SukkoPera/LittleSixteen/doc/6529_replacement_for_C16.gif

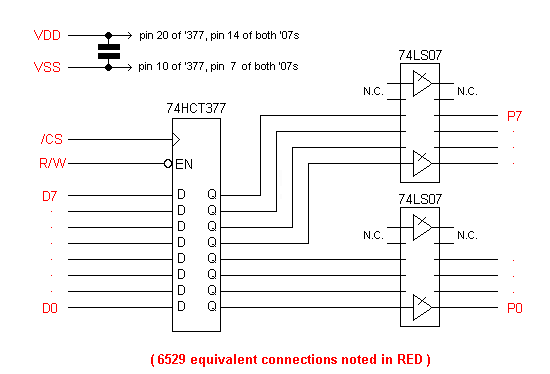
doc/6529_replacement_for_C16.gif
