SukkoPera/LittleSixteen/doc/c16-251788-1of3-left.gif

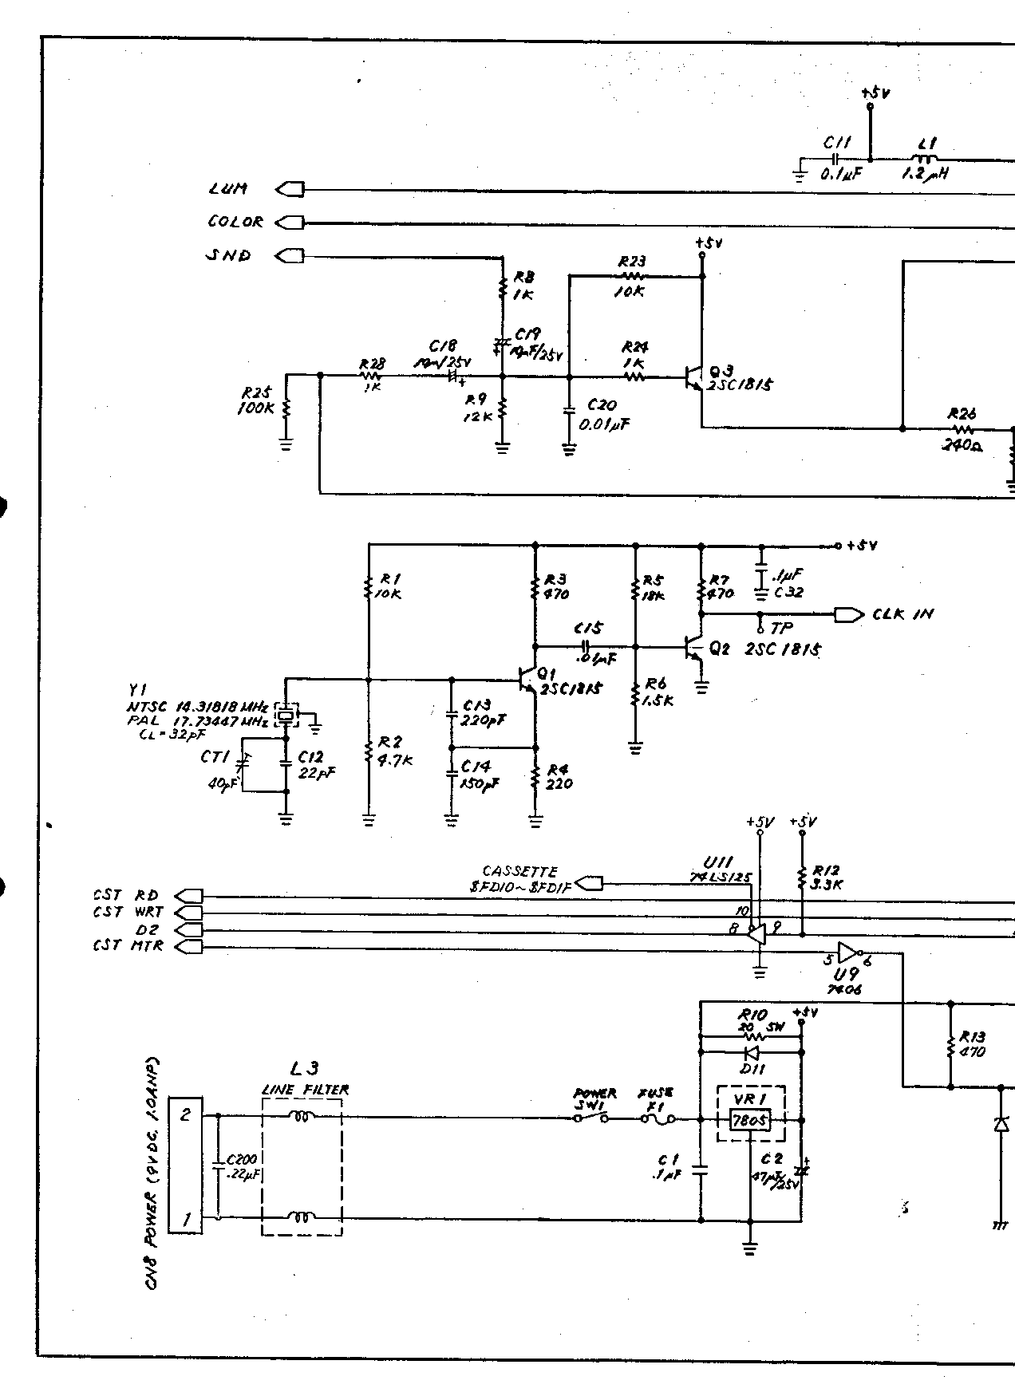
doc/c16-251788-1of3-left.gif
