SukkoPera/LittleSixteen/doc/c16-251788-1of3-right.gif

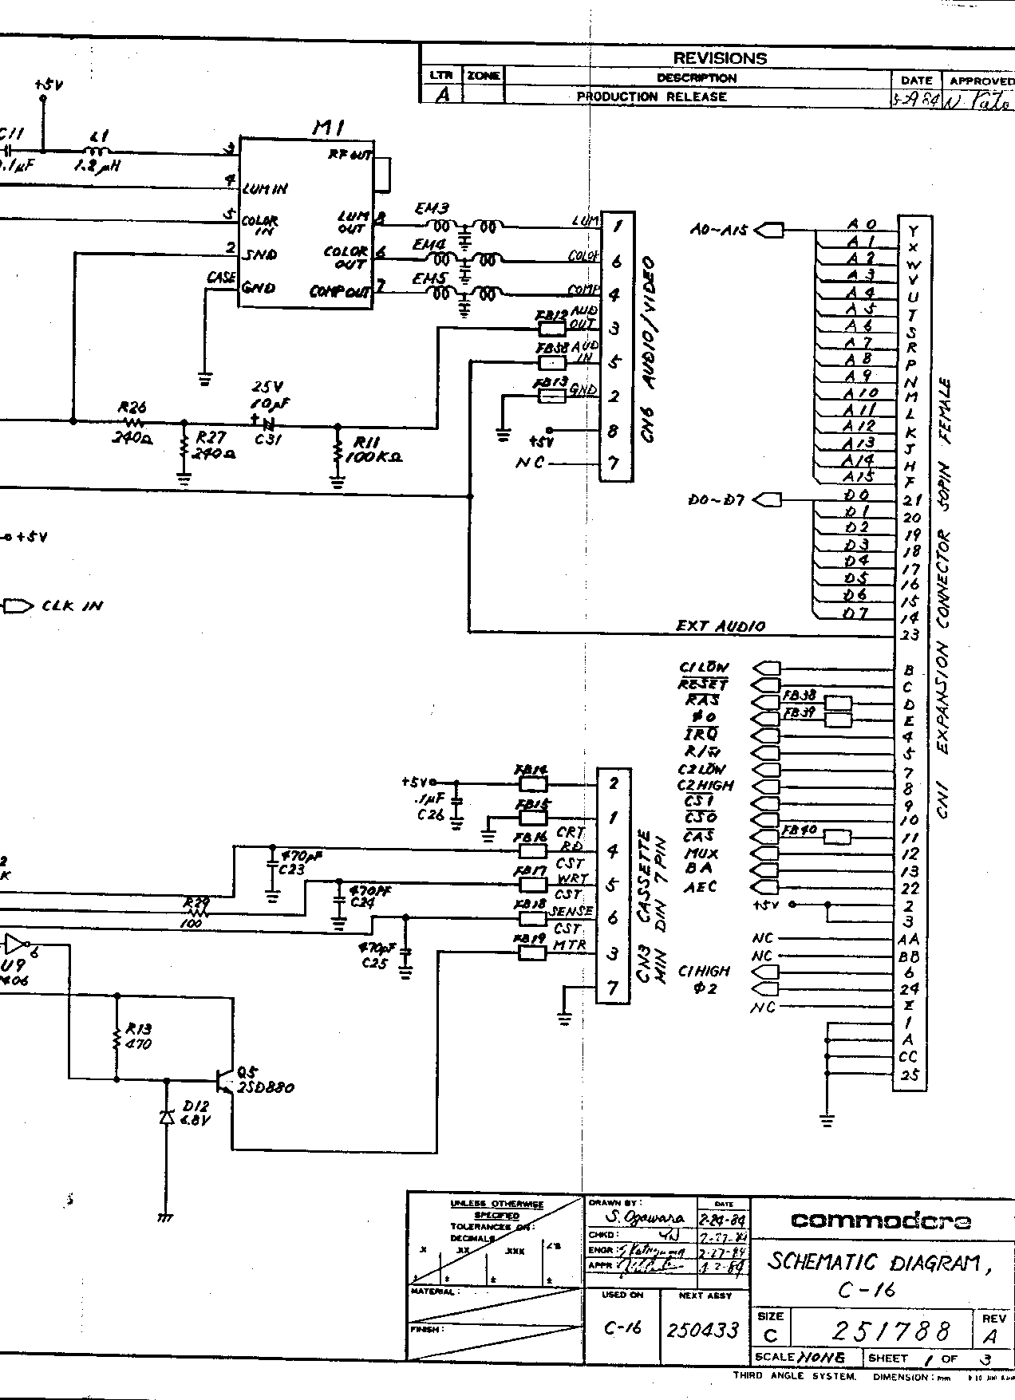
doc/c16-251788-1of3-right.gif
