SukkoPera/LittleSixteen/doc/c16-251788-2of3-right.gif

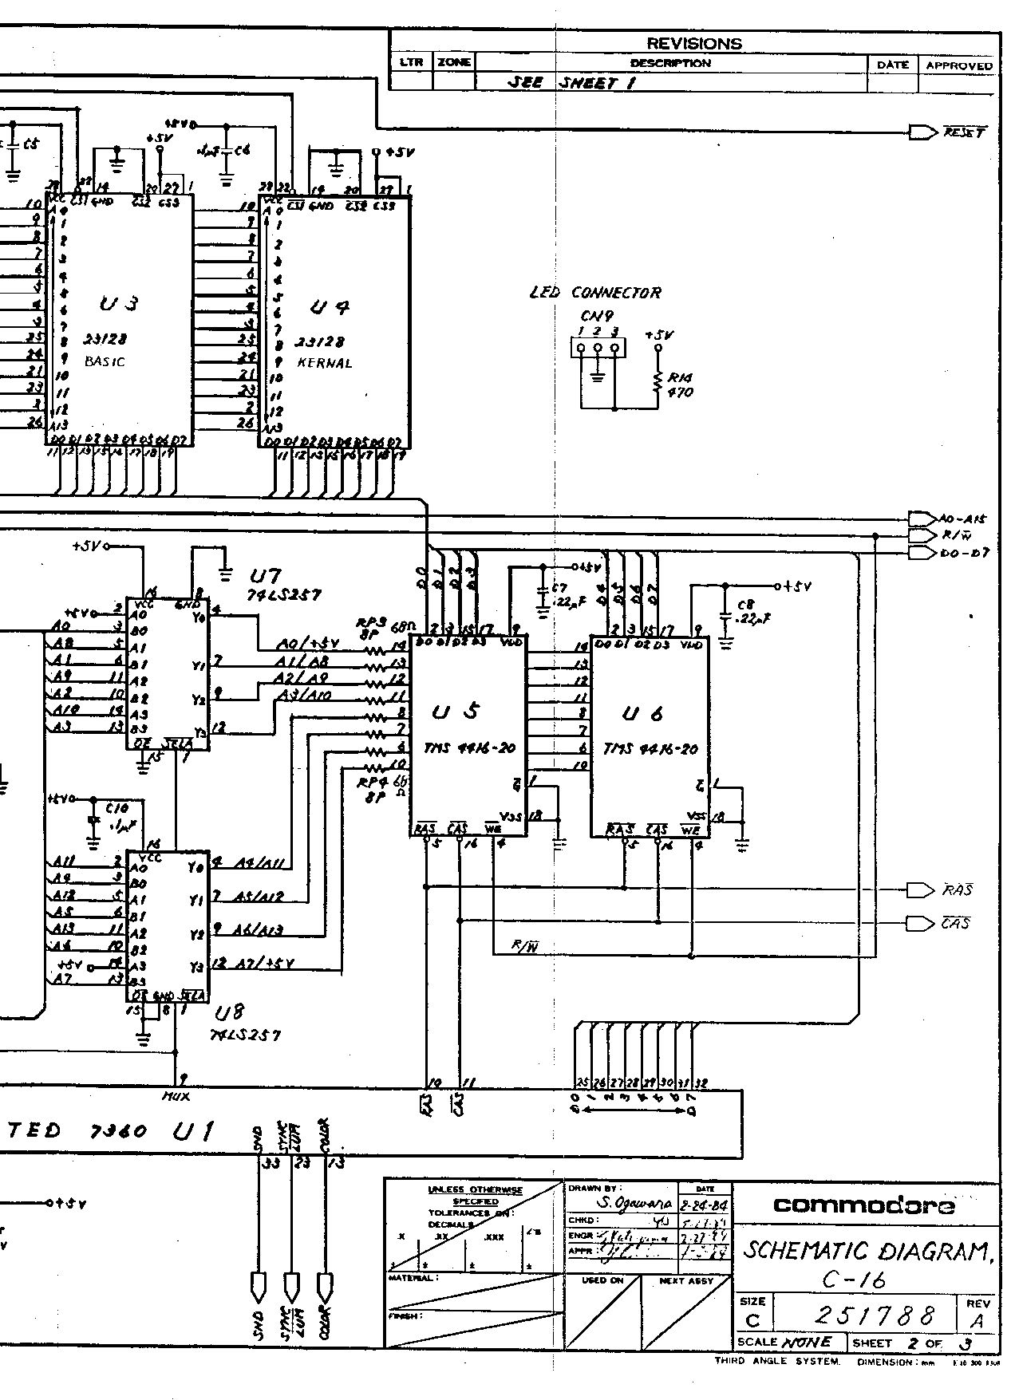
doc/c16-251788-2of3-right.gif
