SukkoPera/LittleSixteen/doc/c16-251788-3of3-right.gif

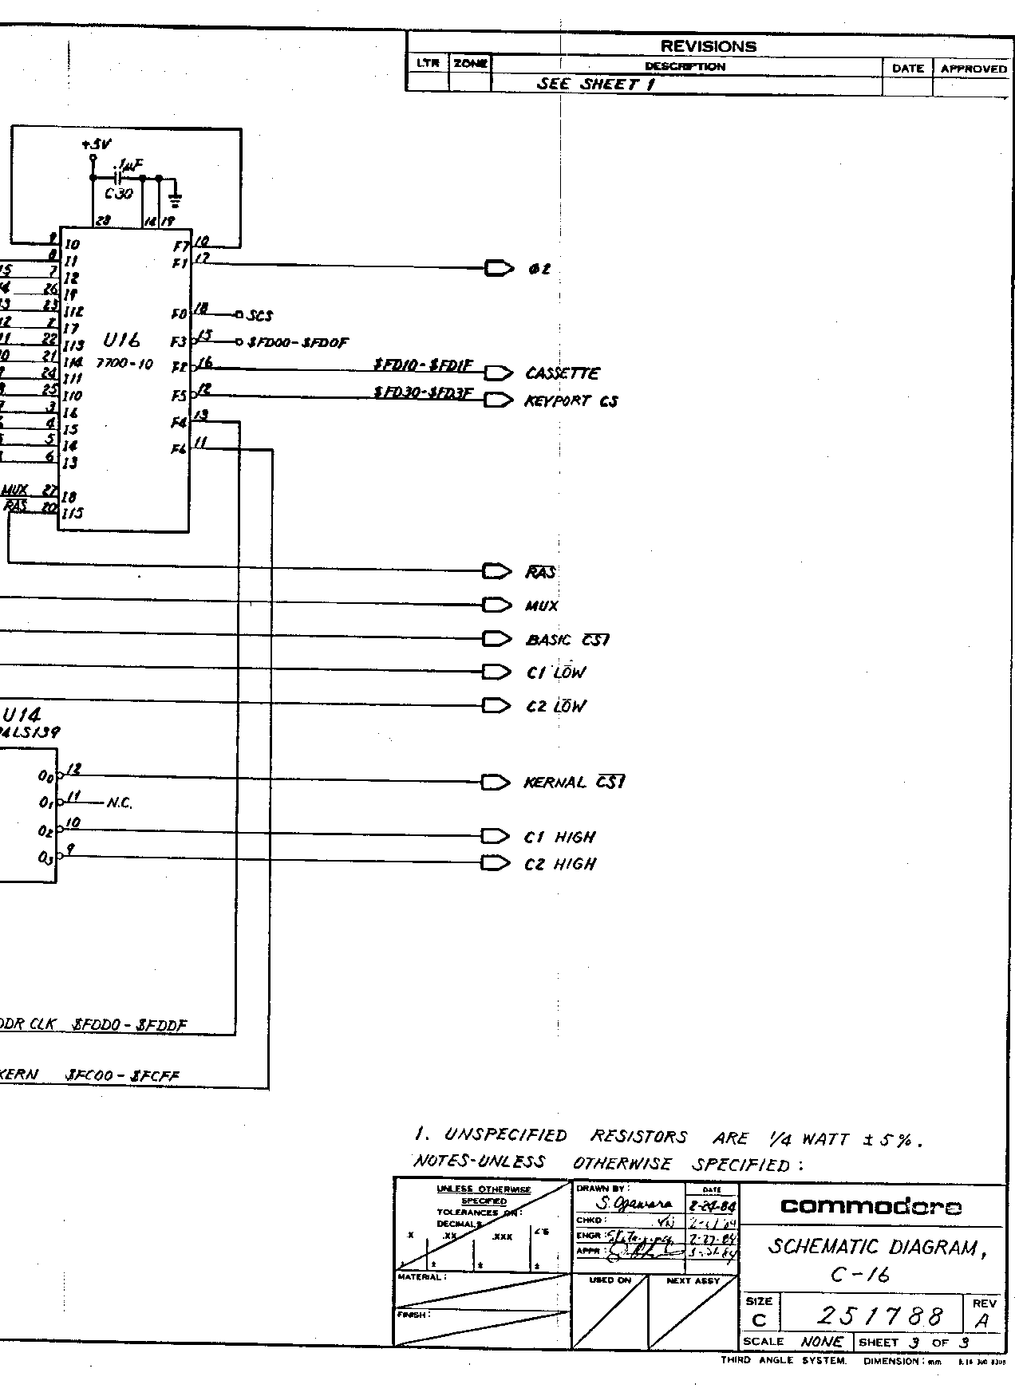
doc/c16-251788-3of3-right.gif
