SukkoPera/LittleSixteen/doc/c16-251788-title.gif

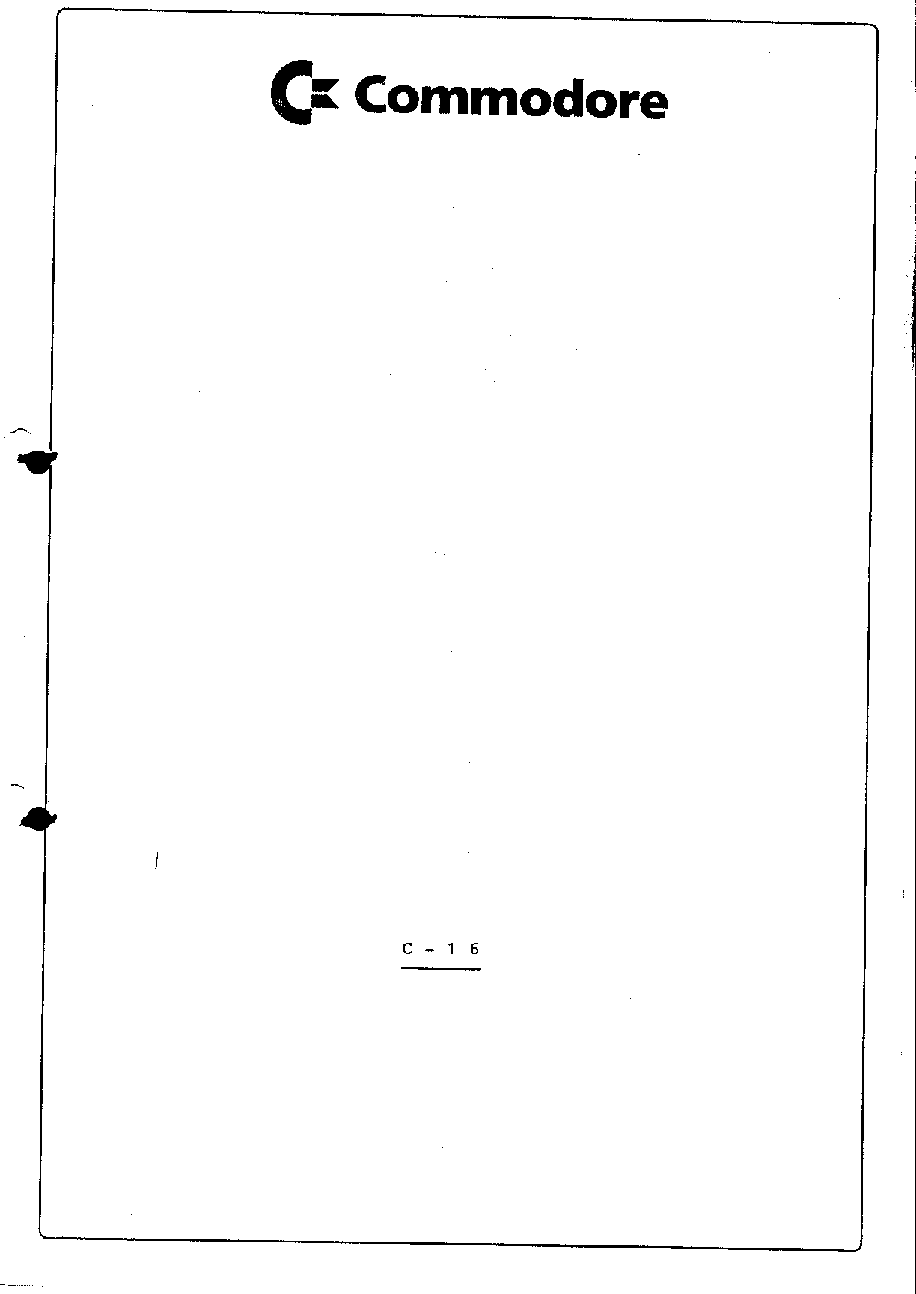
doc/c16-251788-title.gif
