SukkoPera/LittleSixteen/doc/Commodore16_004.jpg

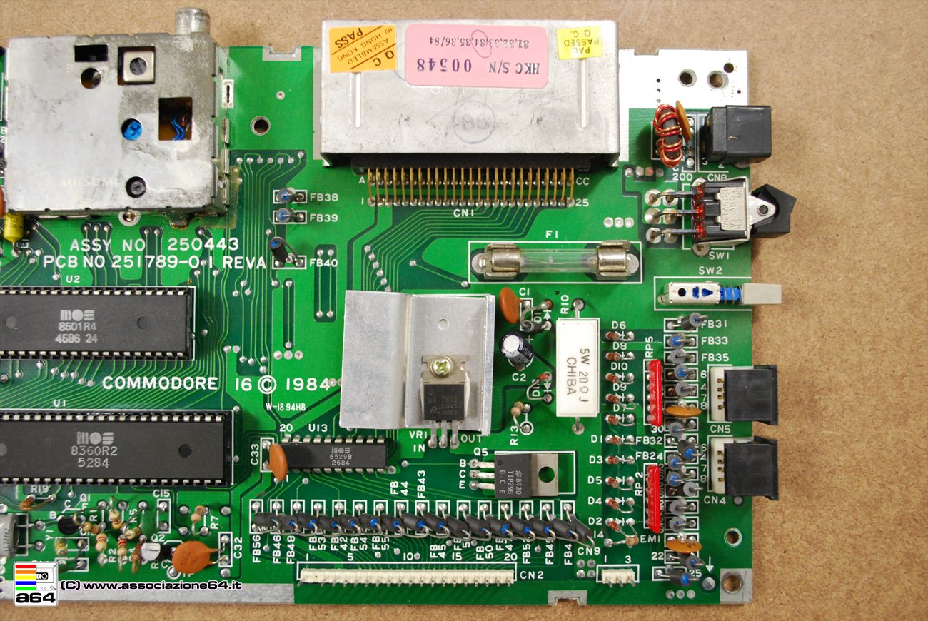
doc/Commodore16_004.jpg
