SukkoPera/LittleSixteen/img/render-bottom.png

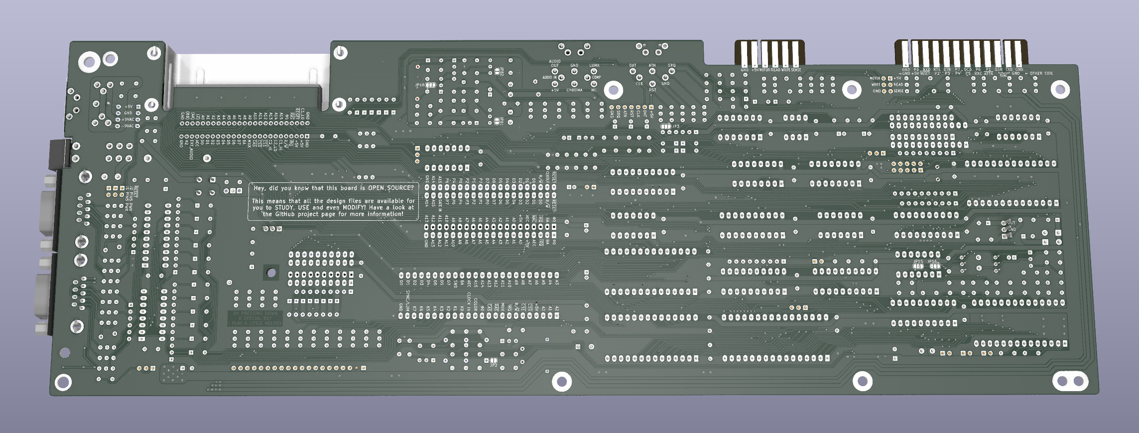
img/render-bottom.png
