SukkoPera/LittleSixteen/LittleSixteen.sch

## KiCad design LittleSixteen.sch (2025-10-18)

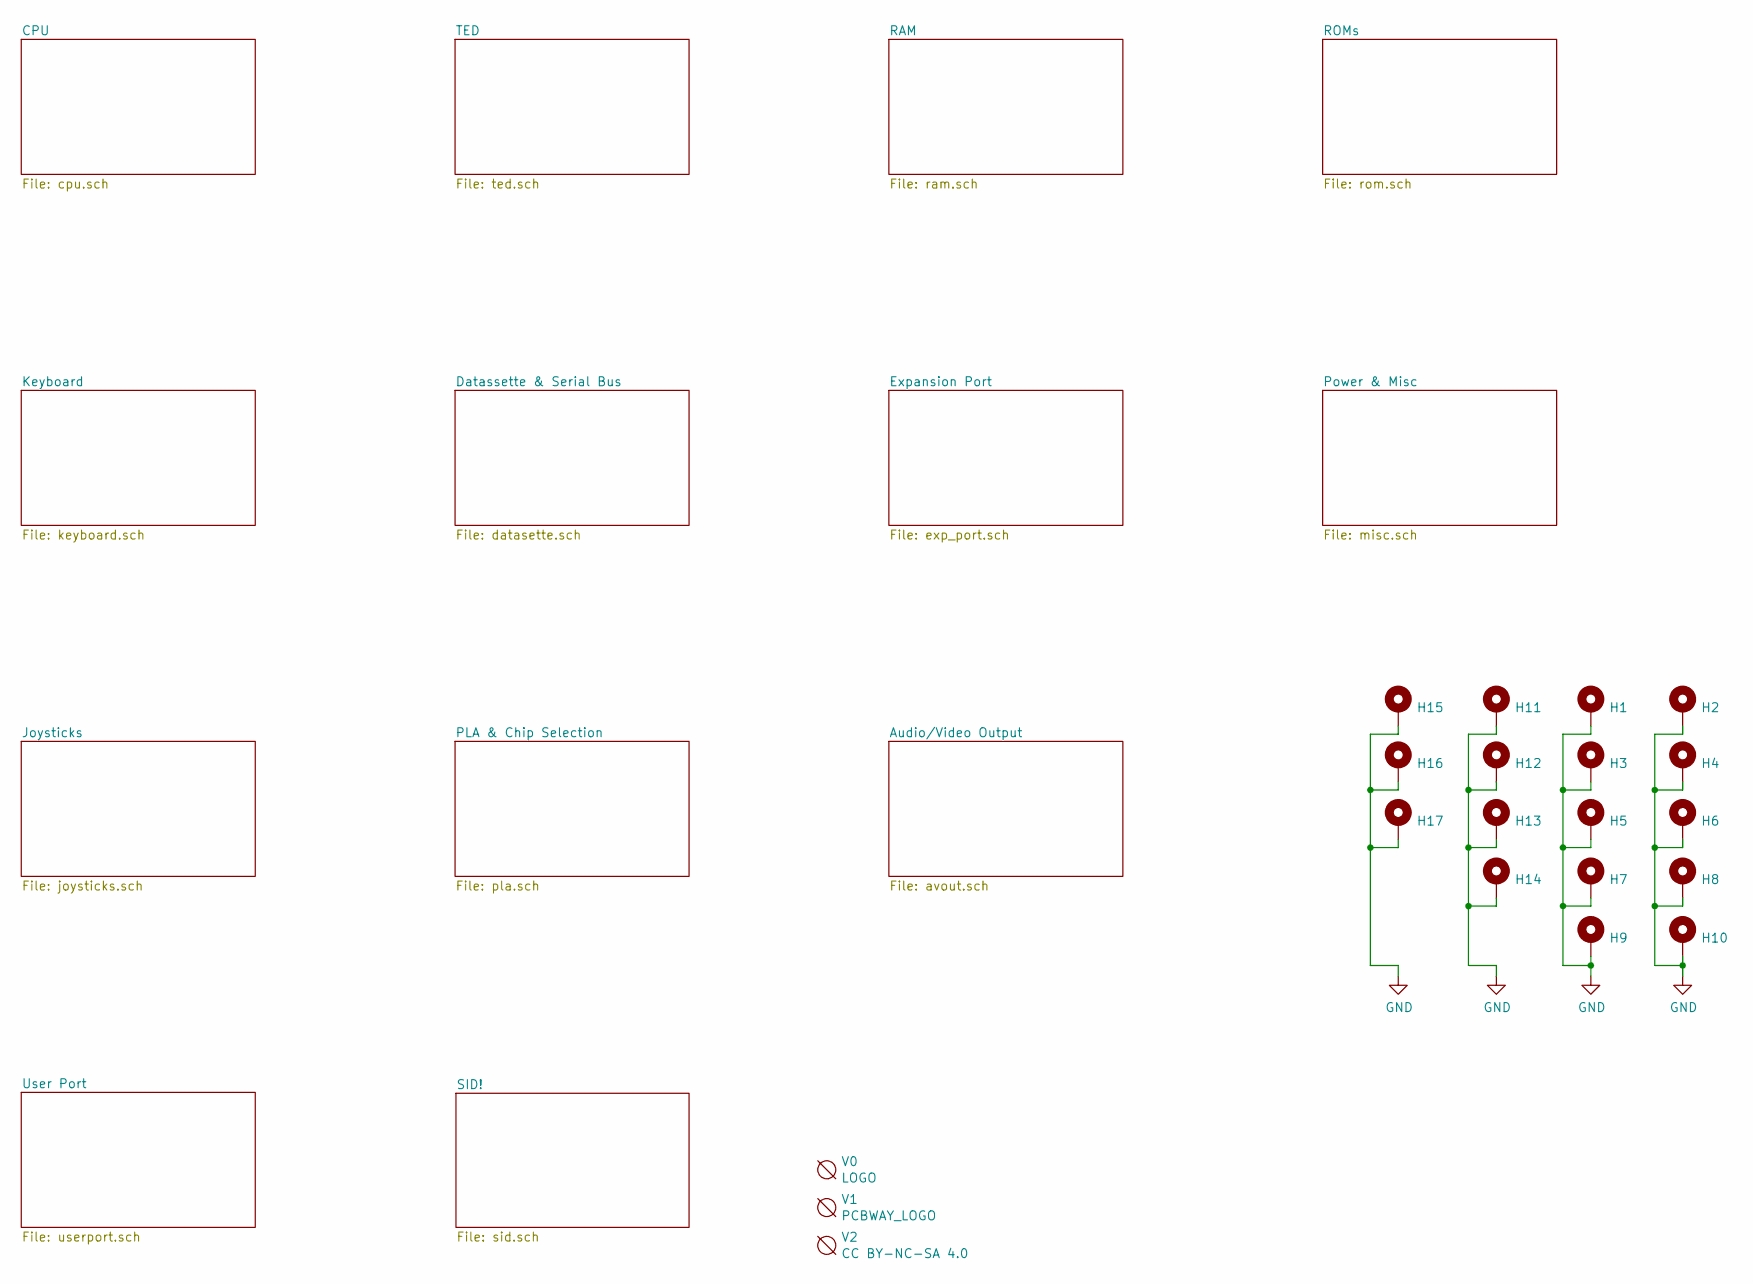
[picture p31: schematic LittleSixteen.sch]

Parts:
H1, H2, H3, H4, H6, H7, H15, H16, H17: MountingHole_Pad; MountingHole_3.7mm_Pad; MouserPN ---
H5, H8: MountingHole_Pad; MouserPN ---
H9, H10: MountingHole_Pad; MountingHole_4.3mm_M4_Pad; MouserPN ---
H11, H12, H13, H14: MountingHole_Pad; MountingHole_2.7mm_Pad; MouserPN ---
V0: LOGO; Logo; MouserPN ---
V1: PCBWAY_LOGO; pcbway; MouserPN ---
V2: CC BY-NC-SA 4.0; cc_by_nc_sa; MouserPN ---

Connections:
GND: H1.1, H2.1, H3.1, H4.1, H5.1, H6.1, H7.1, H8.1, H9.1, H10.1, H11.1, H12.1, H13.1, H14.1, H15.1, H16.1, H17.1
