SukkoPera/LittleSixteen/avout.sch

## KiCad design avout.sch (2025-10-18)

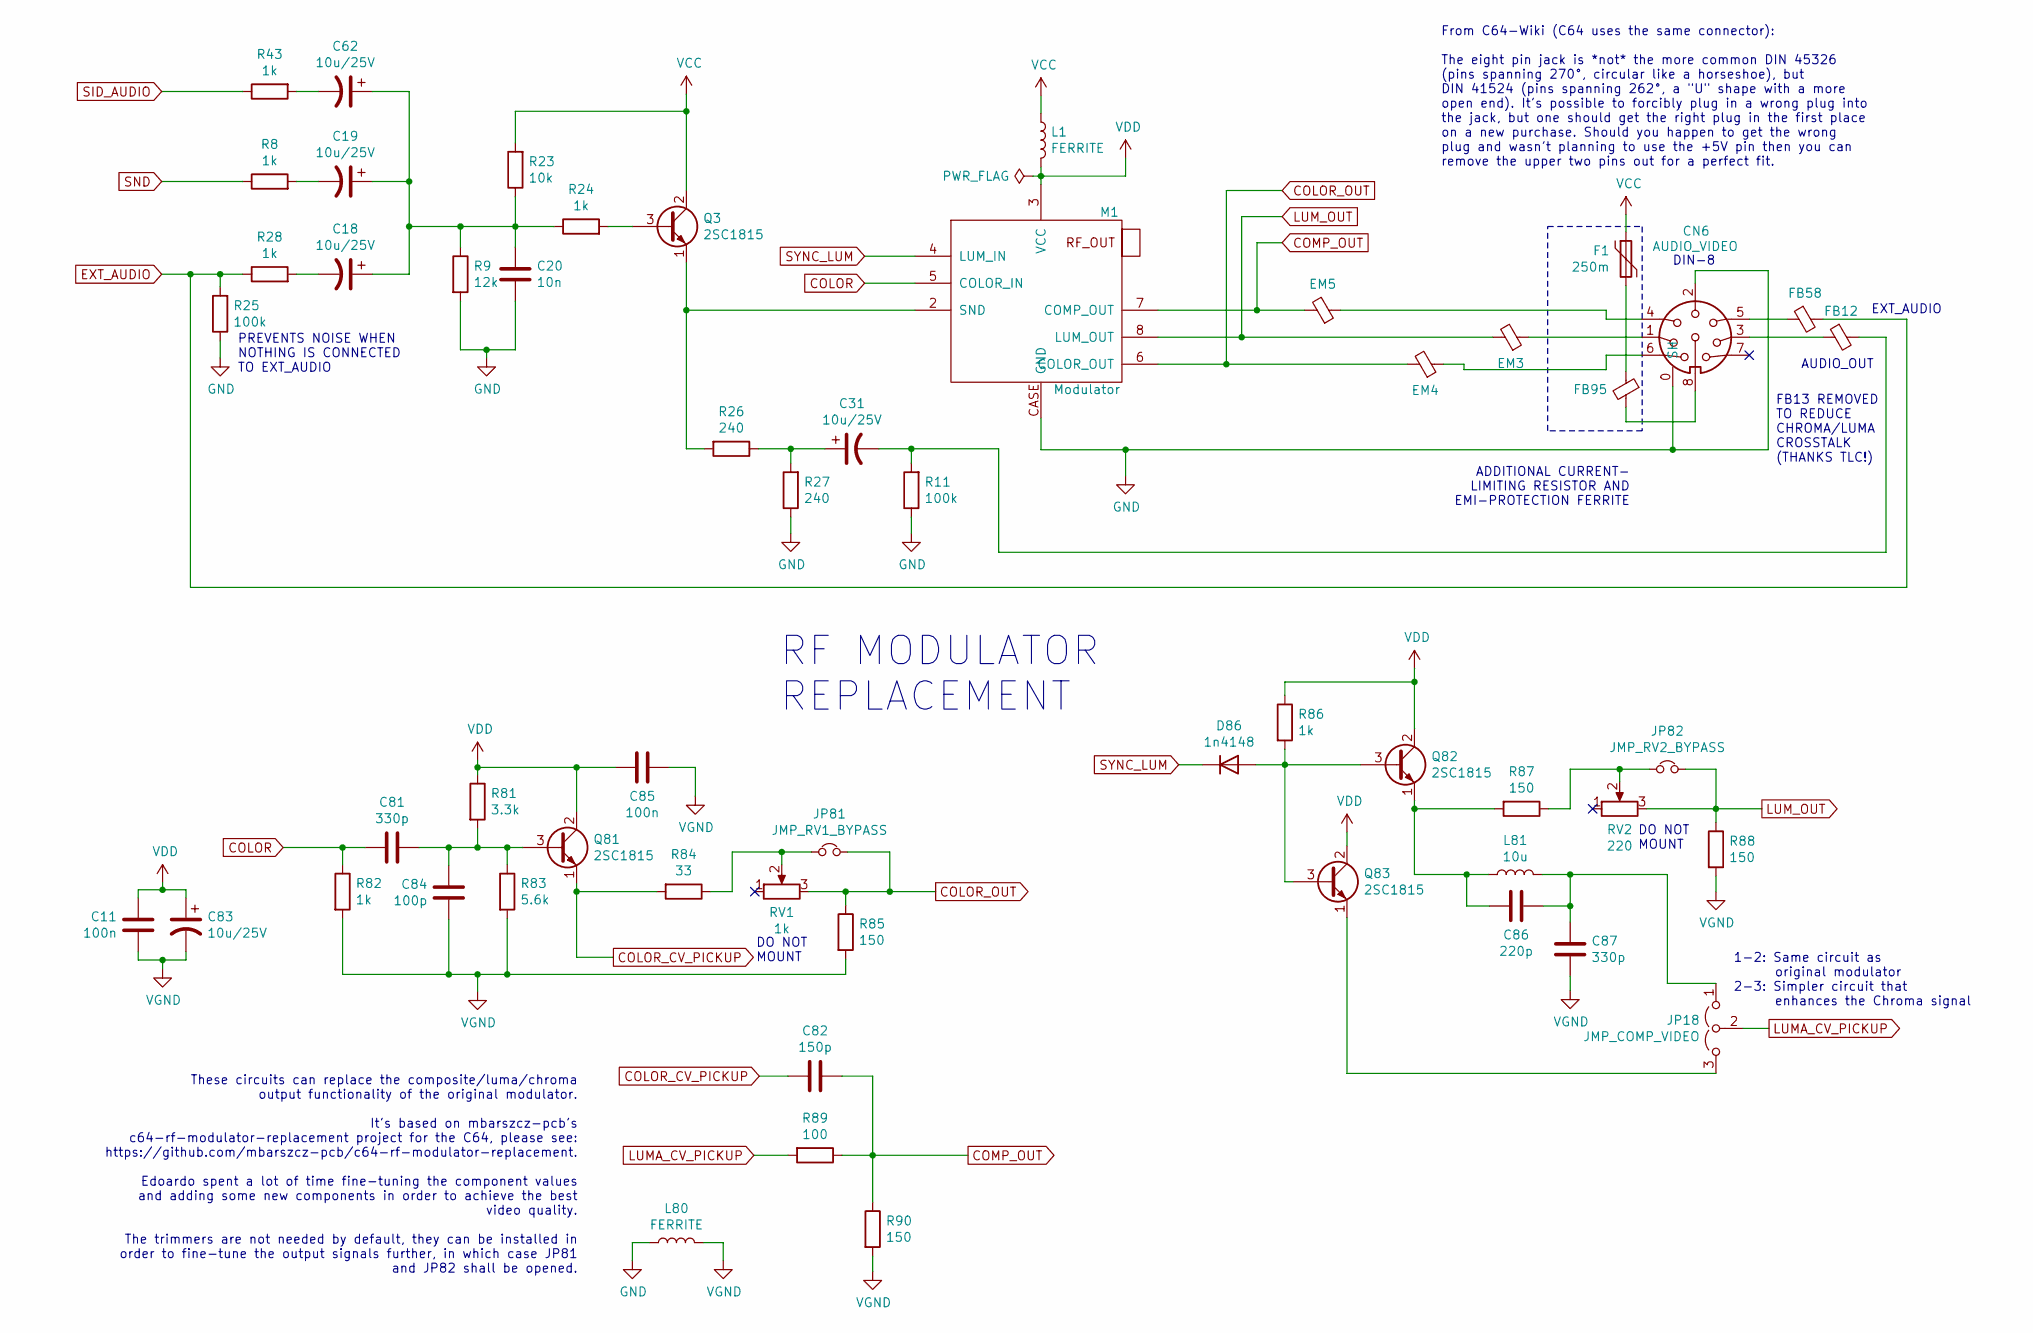
[picture p32: schematic avout.sch]

Parts:
C11, C85: 100n; C_Disc_D8.0mm_W2.5mm_P5.00mm; MouserPN 810-FG28X7R1H104KNT0
C18, C19, C31, C62, C83: 10u/25V; CP_Radial_D5.0mm_P2.00mm; MouserPN 710-860010572002
C20: 10n; C_Disc_D8.0mm_W2.5mm_P5.00mm
C81, C87: 330p; C_Disc_D8.0mm_W2.5mm_P5.00mm
C82: 150p; C_Disc_D8.0mm_W2.5mm_P5.00mm
C84: 100p; C_Disc_D8.0mm_W2.5mm_P5.00mm; MouserPN 810-FG28C0G2A101JNT6
C86: 220p; C_Disc_D8.0mm_W2.5mm_P5.00mm
CN6: AUDIO_VIDEO; DIN-8_DS_8_102_OR_102B
D86: 1n4148; D_DO-35_SOD27_P5.08mm_Vertical_KathodeUp
EM3, EM4, EM5: 270p; EMI_Filter; MouserPN DSS1NB32A271Q91A
F1: 250m; Fuse_Bourns; MouserPN 603-BK60-025-DZ
FB12, FB58, FB95: FERRITE; EMI_Filter; MouserPN 623-2743015112
JP18: JMP_COMP_VIDEO; SolderJumper-3_P1.3mm_Open_RoundedPad1.0x1.5mm; MouserPN ---
JP81: JMP_RV1_BYPASS; SolderJumper-2_P1.3mm_Open_RoundedPad1.0x1.5mm; MouserPN ---
JP82: JMP_RV2_BYPASS; SolderJumper-2_P1.3mm_Open_RoundedPad1.0x1.5mm; MouserPN ---
L1, L80: FERRITE; L_Radial_D6.0mm_P4.00mm; MouserPN 875-28C0236-0EW-10
L81: 10u; L_Axial_L7.0mm_D3.3mm_P12.70mm_Horizontal_Fastron_MICC; MouserPN 871-B78108E1103K000
M1: Modulator; MouserPN ---
Q3, Q81, Q82, Q83: 2SC1815; TO-92_Inline_Wide; MouserPN 610-2SC1815-GR
R8, R24, R28, R43, R82: 1k; R_Axial_DIN0207_L6.3mm_D2.5mm_P5.08mm_Vertical; MouserPN 603-MFR-25FBF52-1K
R9: 12k; R_Axial_DIN0207_L6.3mm_D2.5mm_P5.08mm_Vertical
R11, R25: 100k; R_Axial_DIN0207_L6.3mm_D2.5mm_P5.08mm_Vertical; MouserPN 603-MFR-25FBF52-100K
R23: 10k; R_Axial_DIN0207_L6.3mm_D2.5mm_P5.08mm_Vertical; MouserPN 603-MFR-25FTF52-10K
R26, R27: 240; R_Axial_DIN0207_L6.3mm_D2.5mm_P5.08mm_Vertical
R81: 3.3k; R_Axial_DIN0207_L6.3mm_D2.5mm_P5.08mm_Vertical
R83: 5.6k; R_Axial_DIN0207_L6.3mm_D2.5mm_P5.08mm_Vertical
R84: 33; R_Axial_DIN0207_L6.3mm_D2.5mm_P5.08mm_Vertical
R85, R87, R88, R90: 150; R_Axial_DIN0207_L6.3mm_D2.5mm_P5.08mm_Vertical
R86: 1k; R_Axial_DIN0207_L6.3mm_D2.5mm_P5.08mm_Vertical
R89: 100; R_Axial_DIN0207_L6.3mm_D2.5mm_P5.08mm_Vertical
RV1: 1k; Potentiometer_Bourns_3296W_Vertical; MouserPN 652-3296W-1-102LF
RV2: 220; Potentiometer_Bourns_3296W_Vertical; MouserPN 652-3296W-1-221LF

Connections:
COLOR: C81.2, M1.5 (COLOR_IN), R82.1
COLOR_CV_PICKUP: C82.2, Q81.1 (E), R84.2
COLOR_OUT: EM4.2, JP81.2, M1.6 (COLOR_OUT), R85.1, RV1.3
COMP_OUT: C82.1, EM5.2, M1.7 (COMP_OUT), R89.1, R90.1
EXT_AUDIO: FB58.2, R25.2, R28.1
GND: C20.2, CN6.0 (SH), CN6.2, L80.1, M1.CASE (GND), R9.2, R11.1, R25.1, R27.1
LUMA_CV_PICKUP: JP18.2 (C), R89.2
LUM_OUT: EM3.2, JP82.2, M1.8 (LUM_OUT), R88.1, RV2.3
unnamed: C18.1, C19.1, C20.1, C62.1, R9.1, R23.1, R24.1
unnamed: C18.2, R28.2
unnamed: C19.2, R8.2
unnamed: C31.1, R26.1, R27.2
unnamed: C31.2, FB12.2, R11.2
unnamed: C62.2, R43.2
unnamed: C81.1, C84.2, Q81.3 (B), R81.2, R83.1
unnamed: C86.1, C87.2, JP18.1 (A), L81.2
unnamed: C86.2, L81.1, Q82.1 (E), R87.2
unnamed: CN6.1, EM3.1
unnamed: CN6.3, FB12.1
unnamed: CN6.4, EM5.1
unnamed: CN6.5, FB58.1
unnamed: CN6.6, EM4.1
unnamed: CN6.8, FB95.2
unnamed: D86.2 (A), Q82.3 (B), Q83.3 (B), R86.2
unnamed: F1.2, FB95.1
unnamed: JP18.3 (B), Q83.1 (E)
unnamed: JP81.1, R84.1, RV1.2
unnamed: JP82.1, R87.1, RV2.2
unnamed: M1.2 (SND), Q3.1 (E), R26.2
unnamed: Q3.3 (B), R24.2
SID_AUDIO: R43.1
SND: R8.1
SYNC_LUM: D86.1 (K), M1.4 (LUM_IN)
VCC: F1.1, L1.1, Q3.2 (C), R23.2
VDD: C11.1, C83.1, C85.1, L1.2, M1.3 (VCC), Q81.2 (C), Q82.2 (C), Q83.2 (C), R81.1, R86.1
VGND: C11.2, C83.2, C84.1, C85.2, C87.1, L80.2, R82.2, R83.2, R85.2, R88.2, R90.2

Notes on the sheet:
DIN-8
EXT_AUDIO
AUDIO_OUT
From C64-Wiki (C64 uses the same connector): The eight pin jack is *not* the more common DIN 45326 (pins spanning 270°, circular like a horseshoe), but DIN 41524 (pins spanning 262°, a "U" shape with a more open end). It's possible to forcibly plug in a wrong plug into the jack, but one should get 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
RF MODULATOR REPLACEMENT
These circuits can replace the composite/luma/chroma output functionality of the original modulator. It's based on mbarszcz-pcb's c64-rf-modulator-replacement project for the C64, please see: https://github.com/mbarszcz-pcb/c64-rf-modulator-replacement. Edoardo spent a lot of time fine-tuning the c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
ADDITIONAL CURRENT- LIMITING RESISTOR AND EMI-PROTECTION FERRITE
DO NOT MOUNT
PREVENTS NOISE WHEN NOTHING IS CONNECTED TO EXT_AUDIO
FB13 REMOVED TO REDUCE CHROMA/LUMA CROSSTALK (THANKS TLC!)
1-2: Same circuit as original modulator 2-3: Simpler circuit that enhances the Chroma signal
