SukkoPera/LittleSixteen/cpu.sch

## KiCad design cpu.sch (2025-10-18)

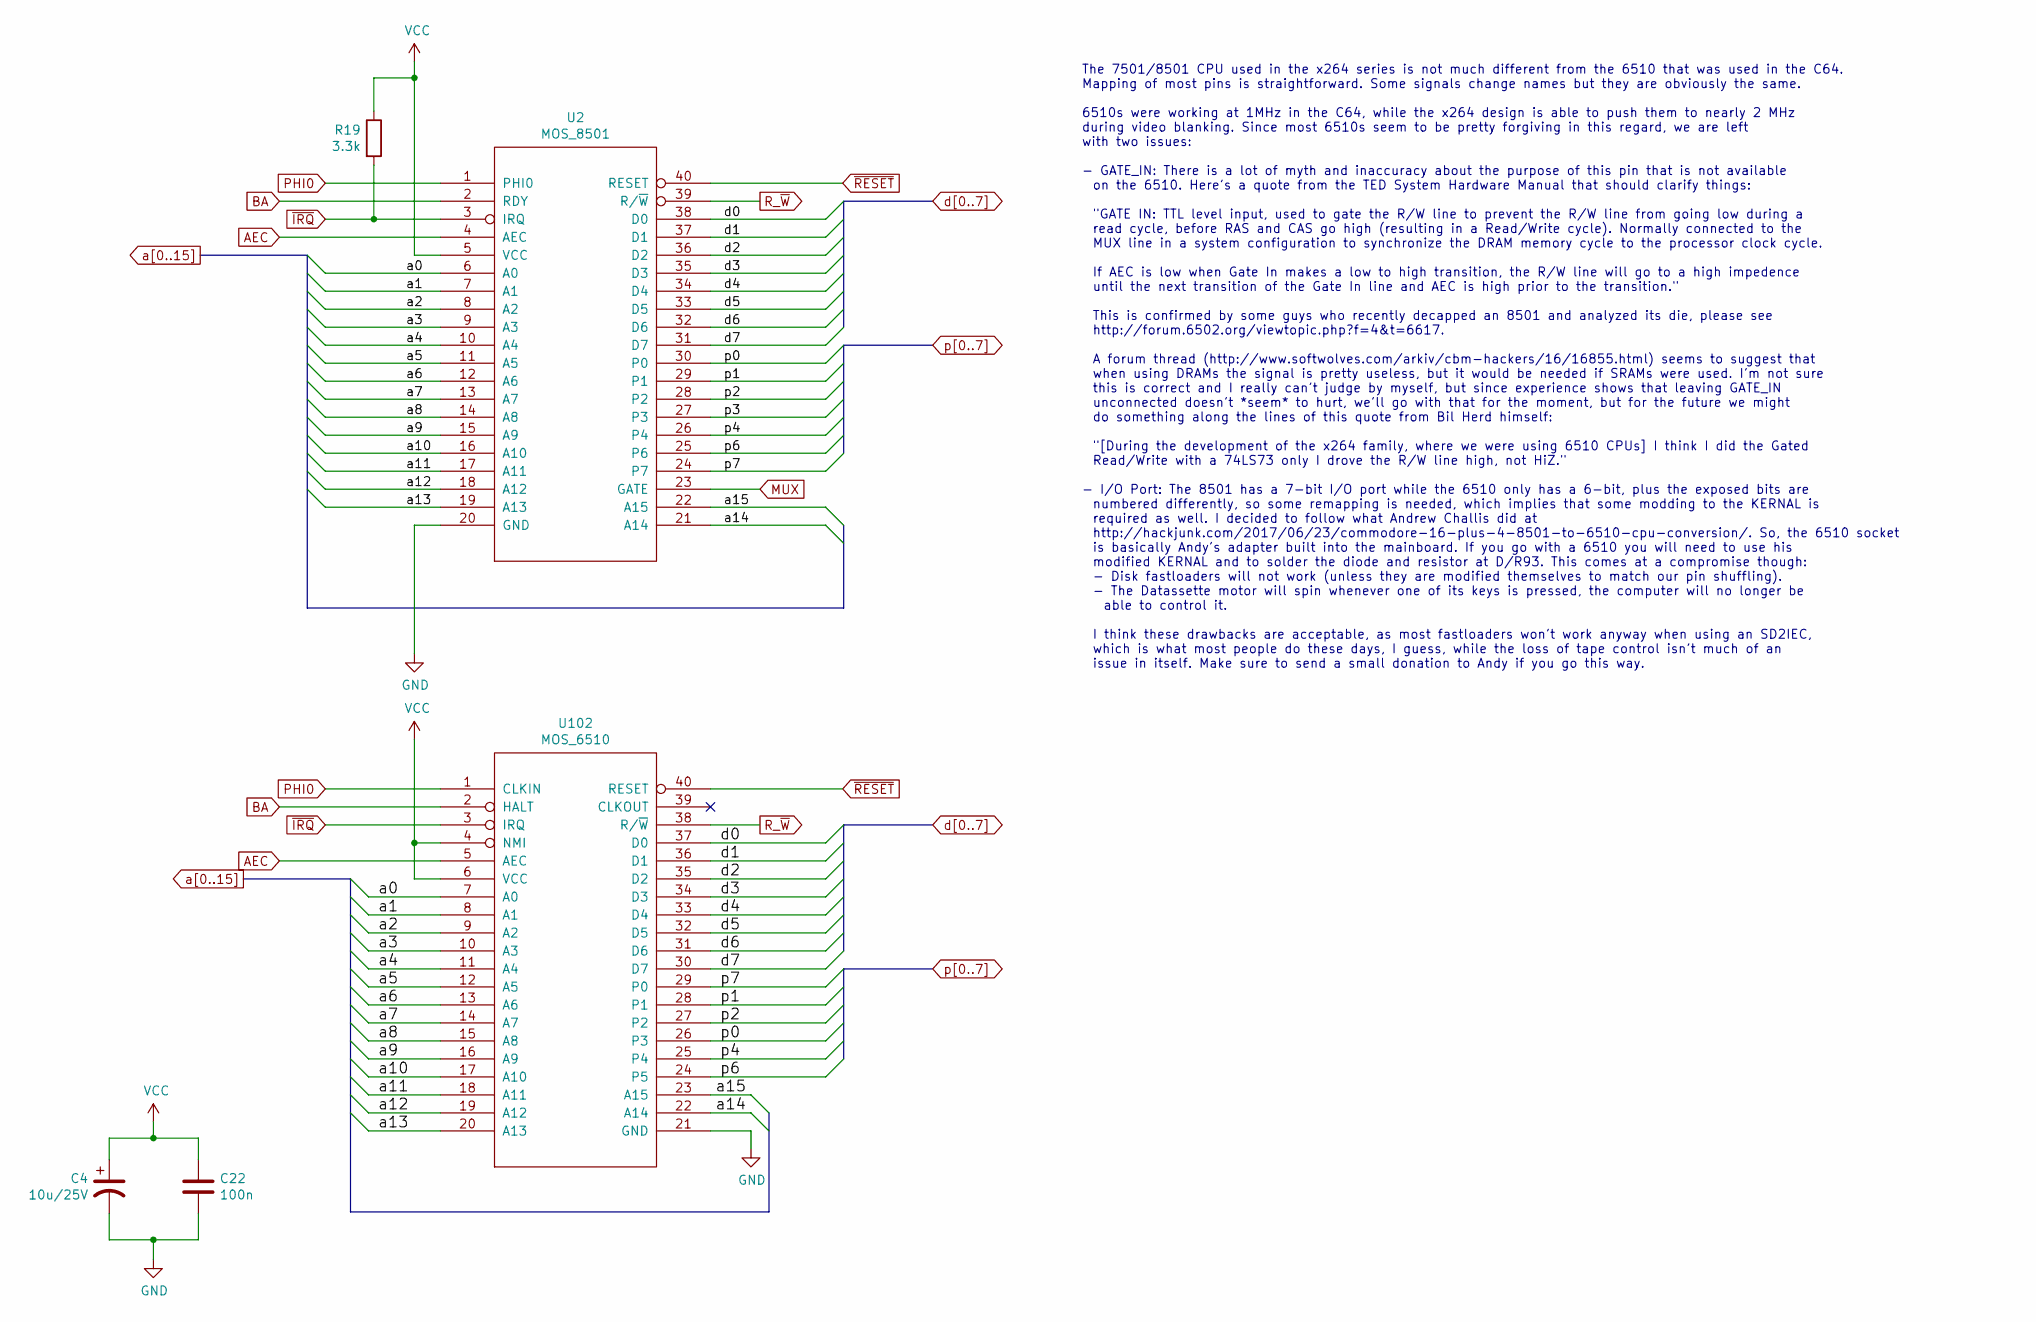
[picture p33: schematic cpu.sch]

Parts:
C4: 10u/25V; CP_Radial_D5.0mm_P2.00mm; MouserPN 710-860010572002
C22: 100n; C_Disc_D8.0mm_W2.5mm_P5.00mm; MouserPN 810-FG28X7R1H104KNT0
R19: 3.3k; R_Axial_DIN0207_L6.3mm_D2.5mm_P5.08mm_Vertical
U2: MOS_8501; DIP-40_W15.24mm_Socket_LongPads; MouserPN :)
U102: MOS_6510; DIP-40_W15.24mm_Socket_LongPads; MouserPN :)

Connections:
AEC: U2.4 (AEC), U102.5 (AEC)
BA: U2.2 (RDY), U102.2 (HALT)
GND: C4.2, C22.2, U2.20 (GND), U102.21 (GND)
MUX: U2.23 (GATE)
PHI0: U2.1 (PHI0), U102.1 (CLKIN)
R_~W: U2.39 (R/~W), U102.38 (R/~W)
VCC: C4.1, C22.1, R19.1, U2.5 (VCC), U102.4 (NMI), U102.6 (VCC)
a0: U2.6 (A0), U102.7 (A0)
a1: U2.7 (A1), U102.8 (A1)
a2: U2.8 (A2), U102.9 (A2)
a3: U2.9 (A3), U102.10 (A3)
a4: U2.10 (A4), U102.11 (A4)
a5: U2.11 (A5), U102.12 (A5)
a6: U2.12 (A6), U102.13 (A6)
a7: U2.13 (A7), U102.14 (A7)
a8: U2.14 (A8), U102.15 (A8)
a9: U2.15 (A9), U102.16 (A9)
a10: U2.16 (A10), U102.17 (A10)
a11: U2.17 (A11), U102.18 (A11)
a12: U2.18 (A12), U102.19 (A12)
a13: U2.19 (A13), U102.20 (A13)
a14: U2.21 (A14), U102.22 (A14)
a15: U2.22 (A15), U102.23 (A15)
d0: U2.38 (D0), U102.37 (D0)
d1: U2.37 (D1), U102.36 (D1)
d2: U2.36 (D2), U102.35 (D2)
d3: U2.35 (D3), U102.34 (D3)
d4: U2.34 (D4), U102.33 (D4)
d5: U2.33 (D5), U102.32 (D5)
d6: U2.32 (D6), U102.31 (D6)
d7: U2.31 (D7), U102.30 (D7)
p0: U2.30 (P0), U102.26 (P3)
p1: U2.29 (P1), U102.28 (P1)
p2: U2.28 (P2), U102.27 (P2)
p3: U2.27 (P3)
p4: U2.26 (P4), U102.25 (P4)
p6: U2.25 (P6), U102.24 (P5)
p7: U2.24 (P7), U102.29 (P0)
~IRQ: R19.2, U2.3 (IRQ), U102.3 (IRQ)
~RESET: U2.40 (RESET), U102.40 (RESET)

Notes on the sheet:
The 7501/8501 CPU used in the x264 series is not much different from the 6510 that was used in the C64. Mapping of most pins is straightforward. Some signals change names but they are obviously the same. 6510s were working at 1MHz in the C64, while the x264 design is able to push them to nearly 2 M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
