SukkoPera/LittleSixteen/datasette.sch

## KiCad design datasette.sch (2025-10-18)

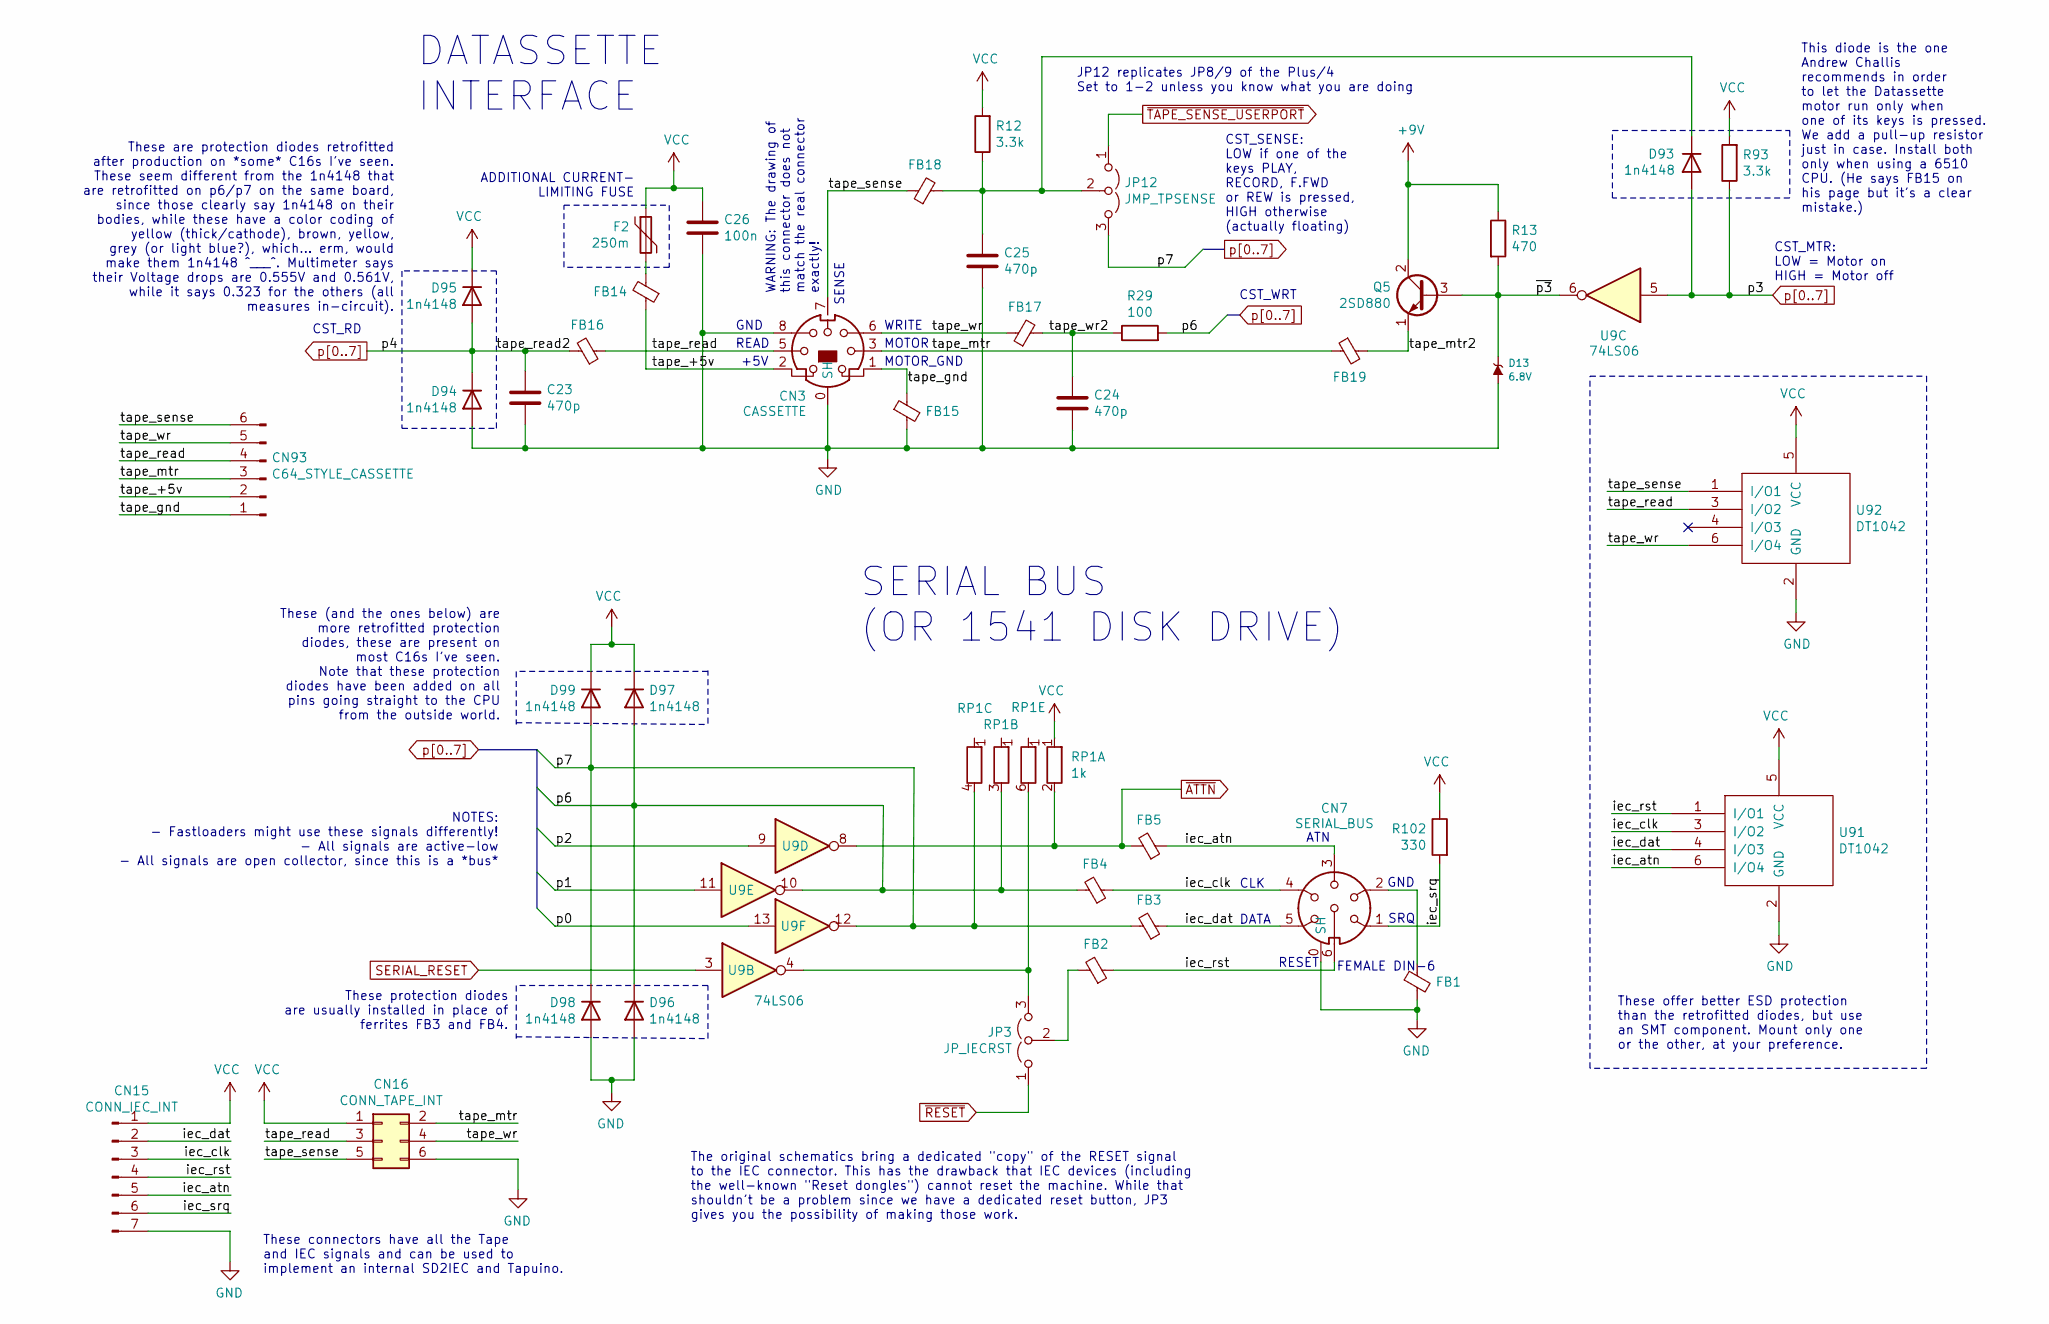
[picture p34: schematic datasette.sch]

Parts:
C23, C24, C25: 470p; C_Disc_D8.0mm_W2.5mm_P5.00mm; MouserPN 810-FG28C0G1H471JNT6
C26: 100n; C_Disc_D8.0mm_W2.5mm_P5.00mm; MouserPN 810-FG28X7R1H104KNT0
CN3: CASSETTE
CN7: SERIAL_BUS; DIN-6_DS_6_102_OR_102B
CN15: CONN_IEC_INT; PinHeader_1x07_P2.54mm_Vertical
CN16: CONN_TAPE_INT; PinHeader_2x03_P2.54mm_Vertical
CN93: C64_STYLE_CASSETTE; C64-Cassette-Port-Male; MouserPN ---
D13: 6.8V; D_DO-35_SOD27_P5.08mm_Vertical_KathodeUp_Zener
D93, D94, D95, D96, D97, D98, D99: 1n4148; D_DO-35_SOD27_P5.08mm_Vertical_KathodeUp
F2: 250m; Fuse_Bourns; MouserPN 603-BK60-025-DZ
FB1, FB2, FB3, FB4, FB5, FB14, FB15, FB16, FB17, FB18, FB19: FERRITE; EMI_Filter; MouserPN 623-2743015112
JP3: JP_IECRST; SolderJumper-3_P1.3mm_Open_RoundedPad1.0x1.5mm; MouserPN ---
JP12: JMP_TPSENSE; PinHeader_1x03_P2.54mm_Vertical; MouserPN ---
Q5: 2SD880; TO-220-3_Horizontal_TabUp; MouserPN 511-TIP29C
R12, R93: 3.3k; R_Axial_DIN0207_L6.3mm_D2.5mm_P5.08mm_Vertical
R13: 470; R_Axial_DIN0207_L6.3mm_D2.5mm_P5.08mm_Vertical
R29: 100; R_Axial_DIN0207_L6.3mm_D2.5mm_P5.08mm_Vertical; MouserPN 708-RNF14FTD100R
R102: 330; R_Axial_DIN0207_L6.3mm_D2.5mm_P5.08mm_Vertical
RP1: 1k; R_Array_SIP6
U9: 74LS06; DIP-14_W7.62mm_Socket_LongPads
U91, U92: DT1042; TSOP-6_1.65x3.05mm_P0.95mm; MouserPN 621-DT1042-04TS-7

Connections:
+9V: Q5.2 (C), R13.1
GND: C23.1, C24.1, C25.1, C26.1, CN3.0 (SH), CN3.8, CN7.0 (SH), CN15.7, CN16.6, D13.1 (A), D94.2 (A), D96.2 (A), D98.2 (A), FB1.2, FB15.2, U91.2 (GND), U92.2 (GND)
unnamed: C25.2, D93.1 (K), FB18.2, JP12.2 (C), R12.1
unnamed: CN7.2, FB1.1
unnamed: F2.2, FB14.2
unnamed: FB2.2, JP3.2 (C)
unnamed: JP3.3 (B), RP1.6 (R5.2), U9.4
SERIAL_RESET: U9.3
VCC: C26.2, CN15.1, CN16.1, D95.1 (K), D97.1 (K), D99.1 (K), F2.1, R12.2, R93.2, R102.1, RP1.1 (R1.1), U91.5 (VCC), U92.5 (VCC)
iec_atn: CN7.3, CN15.5, FB5.1, U91.6 (I/O4)
iec_clk: CN7.4, CN15.3, FB4.1, U91.3 (I/O2)
iec_dat: CN7.5, CN15.2, FB3.1, U91.4 (I/O3)
iec_rst: CN7.6, CN15.4, FB2.1, U91.1 (I/O1)
iec_srq: CN7.1, CN15.6, R102.2
p0: U9.13
p1: U9.11
p2: U9.9
p6: D96.1 (K), D97.2 (A), FB4.2, R29.2, RP1.3 (R2.2), U9.10
p7: D98.1 (K), D99.2 (A), FB3.2, JP12.3 (B), RP1.4 (R3.2), U9.12
p[0..7]: C23.2, D93.2 (A), D94.1 (K), D95.2 (A), FB16.2, R93.1, U9.5
tape_+5v: CN3.2, CN93.2, FB14.1
tape_gnd: CN3.1, CN93.1, FB15.1
tape_mtr: CN3.3, CN16.2, CN93.3, FB19.1
tape_mtr2: FB19.2, Q5.1 (E)
tape_read: CN3.5, CN16.3, CN93.4, FB16.1, U92.3 (I/O2)
tape_sense: CN3.7, CN16.5, CN93.6, FB18.1, U92.1 (I/O1)
tape_wr: CN3.6, CN16.4, CN93.5, FB17.1, U92.6 (I/O4)
tape_wr2: C24.2, FB17.2, R29.1
~ATTN: FB5.2, RP1.2 (R1.2), U9.8
~RESET: JP3.1 (A)
~TAPE_SENSE_USERPORT: JP12.1 (A)
~p3: D13.2 (K), Q5.3 (B), R13.2, U9.6

Notes on the sheet:
CST_MTR: LOW = Motor on HIGH = Motor off
FEMALE DIN-6
SERIAL BUS (OR 1541 DISK DRIVE)
DATASSETTE INTERFACE
CST_WRT
SENSE
WRITE
MOTOR
MOTOR_GND
GND
READ
+5V
These are protection diodes retrofitted after production on *some* C16s I've seen. These seem different from the 1n4148 that are retrofitted on p6/p7 on the same board, since those clearly say 1n4148 on their bodies, while these have a color coding of yellow (thick/cathode), brown, yellow, grey (or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
SRQ
RESET
CST_RD
These (and the ones below) are more retrofitted protection diodes, these are present on most C16s I've seen. Note that these protection diodes have been added on all pins going straight to the CPU from the outside world.
WARNING: The drawing of this connector does not match the real connector exactly!
These protection diodes are usually installed in place of ferrites FB3 and FB4.
This diode is the one Andrew Challis recommends in order to let the Datassette motor run only when one of its keys is pressed. We add a pull-up resistor just in case. Install both only when using a 6510 CPU. (He says FB15 on his page but it's a clear mistake.)
These offer better ESD protection than the retrofitted diodes, but use an SMT component. Mount only one or the other, at your preference.
DATA
CLK
ATN
ADDITIONAL CURRENT- LIMITING FUSE
CST_SENSE: LOW if one of the keys PLAY, RECORD, F.FWD or REW is pressed, HIGH otherwise (actually floating)
These connectors have all the Tape and IEC signals and can be used to implement an internal SD2IEC and Tapuino.
JP12 replicates JP8/9 of the Plus/4 Set to 1-2 unless you know what you are doing
NOTES: - Fastloaders might use these signals differently! - All signals are active-low - All signals are open collector, since this is a *bus*
The original schematics bring a dedicated "copy" of the RESET signal to the IEC connector. This has the drawback that IEC devices (including the well-known "Reset dongles") cannot reset the machine. While that shouldn't be a problem since we have a dedicated reset button, JP3 gives you the possibil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
