SukkoPera/LittleSixteen/exp_port.sch

## KiCad design exp_port.sch (2025-10-18)

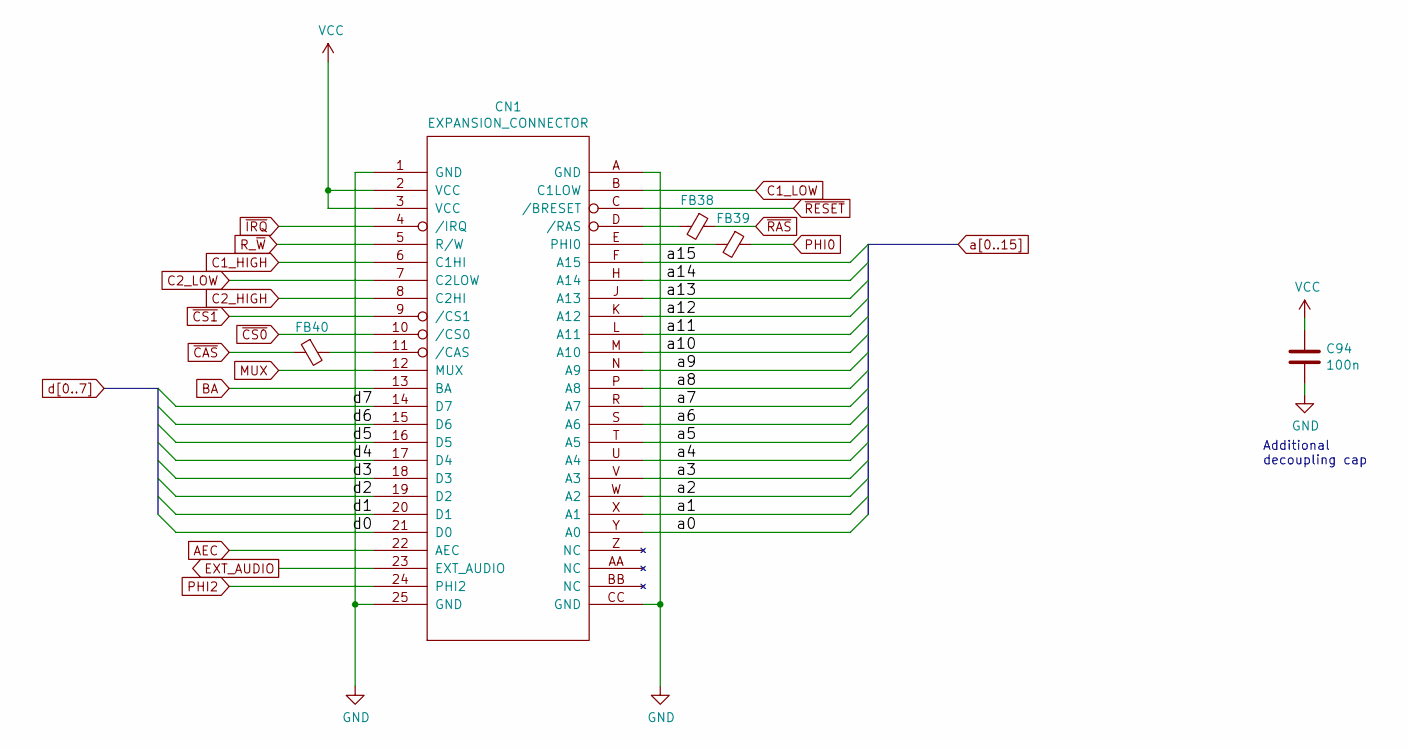
[picture p35: schematic exp_port.sch]

Parts:
C94: 100n; C_Disc_D8.0mm_W2.5mm_P5.00mm; MouserPN 810-FG28X7R1H104KNT0
CN1: EXPANSION_CONNECTOR; 50Pin_Edge_Connector; MouserPN :)
FB38, FB39, FB40: DO NOT MOUNT; EMI_Filter; MouserPN ---

Connections:
AEC: CN1.22 (AEC)
BA: CN1.13 (BA)
C1_HIGH: CN1.6 (C1HI)
C1_LOW: CN1.B (C1LOW)
C2_HIGH: CN1.8 (C2HI)
C2_LOW: CN1.7 (C2LOW)
EXT_AUDIO: CN1.23 (EXT_AUDIO)
GND: C94.2, CN1.1 (GND), CN1.25 (GND), CN1.A (GND), CN1.CC (GND)
MUX: CN1.12 (MUX)
unnamed: CN1.11 (/CAS), FB40.2
unnamed: CN1.D (/RAS), FB38.2
unnamed: CN1.E (PHI0), FB39.2
PHI0: FB39.1
PHI2: CN1.24 (PHI2)
R_~W: CN1.5 (R/W)
VCC: C94.1, CN1.2 (VCC), CN1.3 (VCC)
a0: CN1.Y (A0)
a1: CN1.X (A1)
a2: CN1.W (A2)
a3: CN1.V (A3)
a4: CN1.U (A4)
a5: CN1.T (A5)
a6: CN1.S (A6)
a7: CN1.R (A7)
a8: CN1.P (A8)
a9: CN1.N (A9)
a10: CN1.M (A10)
a11: CN1.L (A11)
a12: CN1.K (A12)
a13: CN1.J (A13)
a14: CN1.H (A14)
a15: CN1.F (A15)
d0: CN1.21 (D0)
d1: CN1.20 (D1)
d2: CN1.19 (D2)
d3: CN1.18 (D3)
d4: CN1.17 (D4)
d5: CN1.16 (D5)
d6: CN1.15 (D6)
d7: CN1.14 (D7)
~CAS: FB40.1
~CS0: CN1.10 (/CS0)
~CS1: CN1.9 (/CS1)
~IRQ: CN1.4 (/IRQ)
~RAS: FB38.1
~RESET: CN1.C (/BRESET)

Notes on the sheet:
Additional decoupling cap
