SukkoPera/LittleSixteen/joysticks.sch

## KiCad design joysticks.sch (2025-10-18)

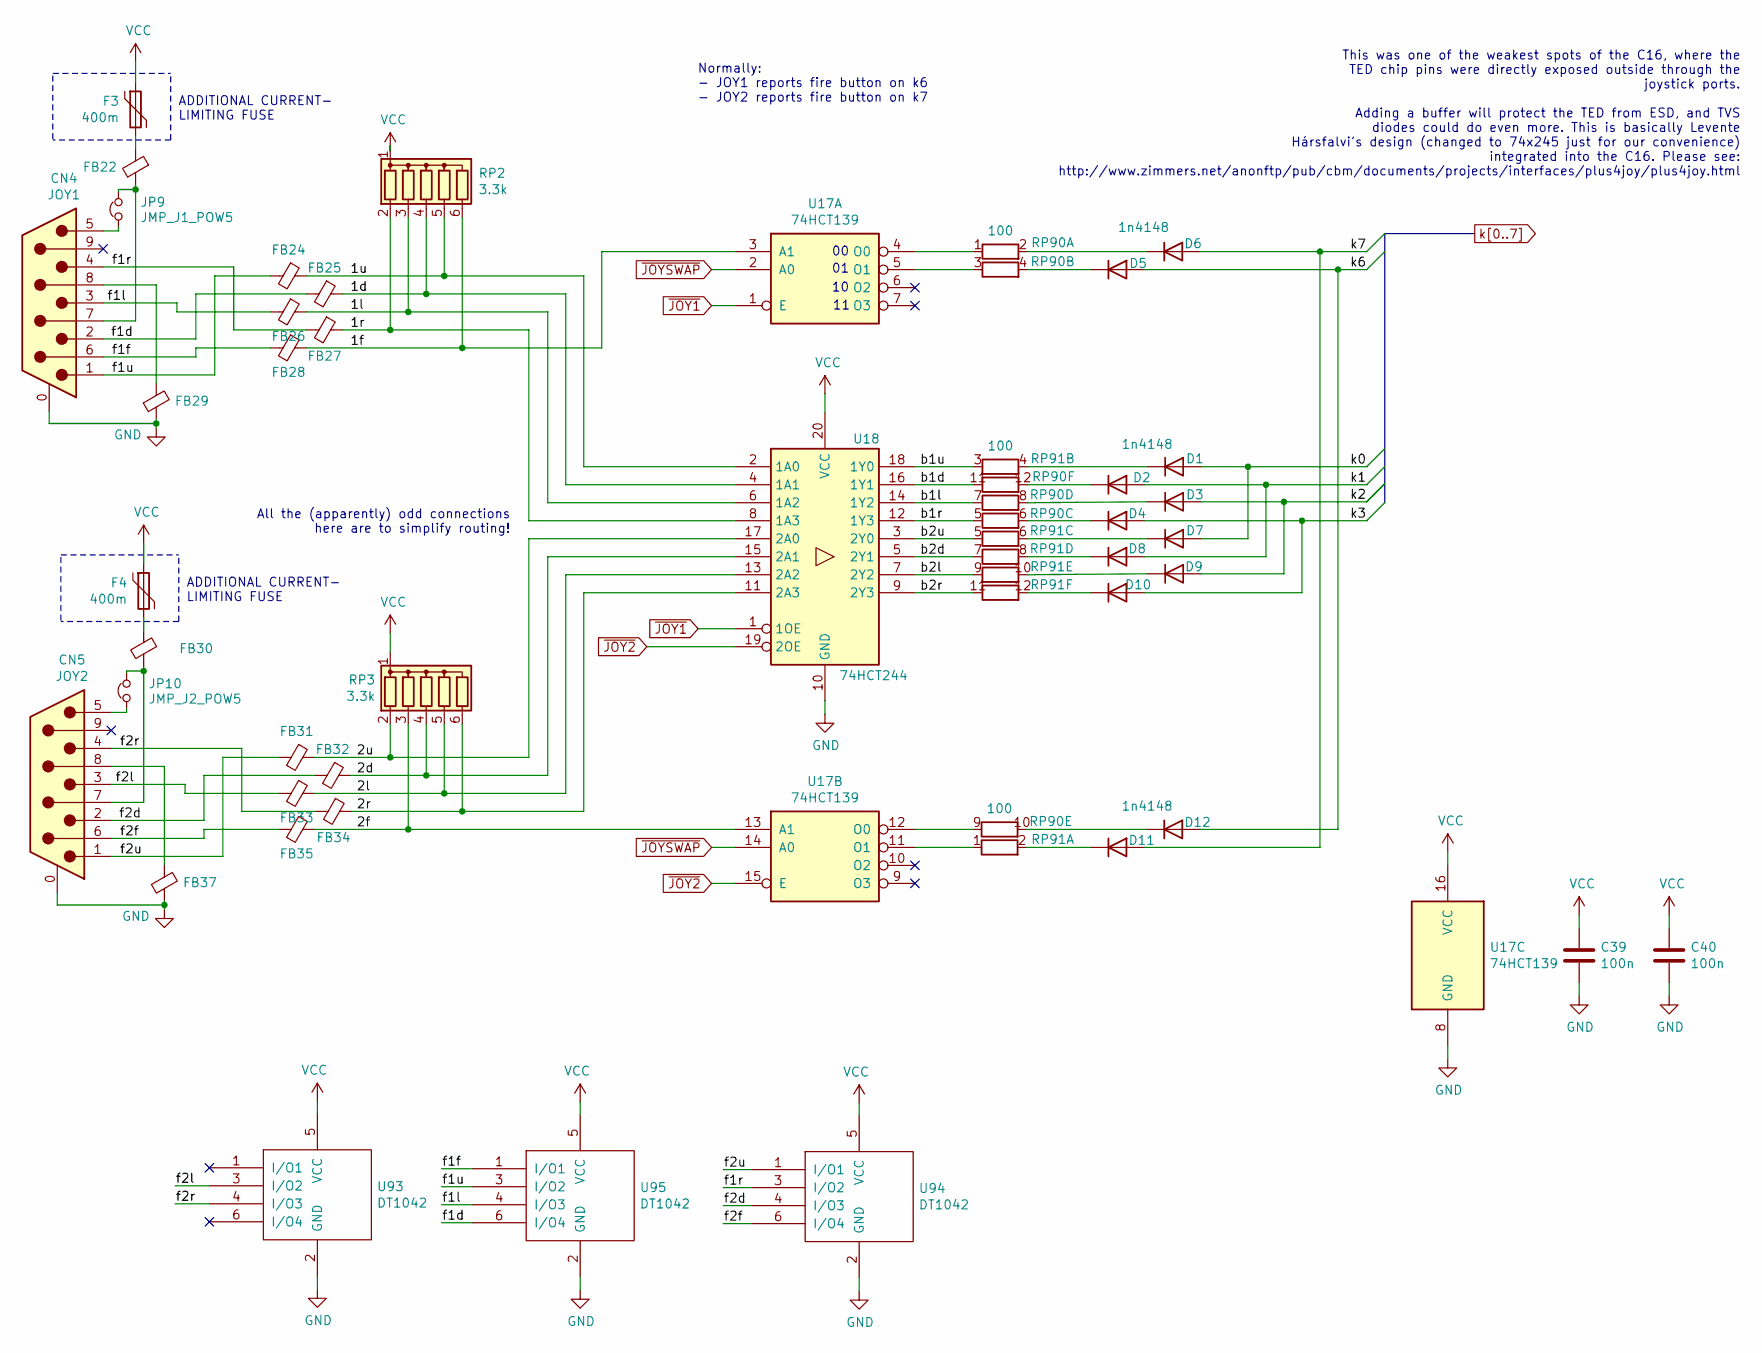
[picture p36: schematic joysticks.sch]

Parts:
C39, C40: 100n; C_Disc_D8.0mm_W2.5mm_P5.00mm; MouserPN 810-FG28X7R1H104KNT0
CN4: JOY1; DB_9M
CN5: JOY2; DB_9M
D1, D2, D3, D4, D5, D6, D7, D8, D9, D10, D11, D12: 1n4148; D_DO-35_SOD27_P5.08mm_Vertical_KathodeUp
F3, F4: 400m; Fuse_Bourns; MouserPN 603-BK60-040-DI
FB22, FB24, FB25, FB26, FB27, FB28, FB29, FB30, FB31, FB32, FB33, FB34, FB35, FB37: FERRITE; EMI_Filter; MouserPN 623-2743015112
JP9: JMP_J1_POW5; PinHeader_1x02_P2.54mm_Vertical
JP10: JMP_J2_POW5; PinHeader_1x02_P2.54mm_Vertical
RP2, RP3: 3.3k; R_Array_SIP6; MouserPN 774-77061332P
RP90, RP91: 100; R_Array_SIP12; MouserPN 652-4612X-2LF-100
U17: 74HCT139; DIP-16_W7.62mm_Socket_LongPads; MouserPN 595-SN74HCT139N
U18: 74HCT244; DIP-20_W7.62mm_Socket_LongPads; MouserPN 595-CD74HCT244E
U93, U94, U95: DT1042; TSOP-6_1.65x3.05mm_P0.95mm; MouserPN 621-DT1042-04TS-7

Connections:
1d: FB25.1, RP2.4 (R3), U18.4 (1A1)
1f: FB28.1, RP2.6 (R5), U17.3 (A1)
1l: FB26.1, RP2.3 (R2), U18.6 (1A2)
1r: FB27.1, RP2.2 (R1), U18.8 (1A3)
1u: FB24.1, RP2.5 (R4), U18.2 (1A0)
2d: FB32.1, RP3.4 (R3), U18.15 (2A1)
2f: FB35.1, RP3.3 (R2), U17.13 (A1)
2l: FB33.1, RP3.5 (R4), U18.13 (2A2)
2r: FB34.1, RP3.6 (R5), U18.11 (2A3)
2u: FB31.1, RP3.2 (R1), U18.17 (2A0)
GND: C39.2, C40.2, CN4.0 (PAD), CN5.0 (PAD), FB29.1, FB37.1, U17.8 (GND), U18.10 (GND), U93.2 (GND), U94.2 (GND), U95.2 (GND)
unnamed: CN4.5, JP9.1
unnamed: CN4.7, FB22.2, JP9.2
unnamed: CN4.8, FB29.2
unnamed: CN5.5, JP10.1
unnamed: CN5.7, FB30.2, JP10.2
unnamed: CN5.8, FB37.2
unnamed: D1.1 (K), RP91.4 (R2.2)
unnamed: D2.1 (K), RP90.12 (R6.2)
unnamed: D3.1 (K), RP90.8 (R4.2)
unnamed: D4.1 (K), RP90.6 (R3.2)
unnamed: D5.1 (K), RP90.4 (R2.2)
unnamed: D6.1 (K), RP90.2 (R1.2)
unnamed: D7.1 (K), RP91.6 (R3.2)
unnamed: D8.1 (K), RP91.8 (R4.2)
unnamed: D9.1 (K), RP91.10 (R5.2)
unnamed: D10.1 (K), RP91.12 (R6.2)
unnamed: D11.1 (K), RP91.2 (R1.2)
unnamed: D12.1 (K), RP90.10 (R5.2)
unnamed: F3.2, FB22.1
unnamed: F4.2, FB30.1
unnamed: RP90.1 (R1.1), U17.4 (O0)
unnamed: RP90.3 (R2.1), U17.5 (O1)
unnamed: RP90.9 (R5.1), U17.12 (O0)
unnamed: RP91.1 (R1.1), U17.11 (O1)
VCC: C39.1, C40.1, F3.1, F4.1, RP2.1 (common), RP3.1 (common), U17.16 (VCC), U18.20 (VCC), U93.5 (VCC), U94.5 (VCC), U95.5 (VCC)
b1d: RP90.11 (R6.1), U18.16 (1Y1)
b1l: RP90.7 (R4.1), U18.14 (1Y2)
b1r: RP90.5 (R3.1), U18.12 (1Y3)
b1u: RP91.3 (R2.1), U18.18 (1Y0)
b2d: RP91.7 (R4.1), U18.5 (2Y1)
b2l: RP91.9 (R5.1), U18.7 (2Y2)
b2r: RP91.11 (R6.1), U18.9 (2Y3)
b2u: RP91.5 (R3.1), U18.3 (2Y0)
f1d: CN4.2, FB25.2, U95.6 (I/O4)
f1f: CN4.6, FB28.2, U95.1 (I/O1)
f1l: CN4.3, FB26.2, U95.4 (I/O3)
f1r: CN4.4, FB27.2, U94.3 (I/O2)
f1u: CN4.1, FB24.2, U95.3 (I/O2)
f2d: CN5.2, FB32.2, U94.4 (I/O3)
f2f: CN5.6, FB35.2, U94.6 (I/O4)
f2l: CN5.3, FB33.2, U93.3 (I/O2)
f2r: CN5.4, FB34.2, U93.4 (I/O3)
f2u: CN5.1, FB31.2, U94.1 (I/O1)
k0: D1.2 (A), D7.2 (A)
k1: D2.2 (A), D8.2 (A)
k2: D3.2 (A), D9.2 (A)
k3: D4.2 (A), D10.2 (A)
k6: D5.2 (A), D12.2 (A)
k7: D6.2 (A), D11.2 (A)
~JOY1: U17.1 (E), U18.1 (1OE)
~JOY2: U17.15 (E), U18.19 (2OE)
~JOYSWAP: U17.2 (A0), U17.14 (A0)

Notes on the sheet:
ADDITIONAL CURRENT- LIMITING FUSE
All the (apparently) odd connections here are to simplify routing!
This was one of the weakest spots of the C16, where the TED chip pins were directly exposed outside through the joystick ports. Adding a buffer will protect the TED from ESD, and TVS diodes could do even more. This is basically Levente Hársfalvi's design (changed to 74x245 just for our convenience)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
Normally: - JOY1 reports fire button on k6 - JOY2 reports fire button on k7
