SukkoPera/LittleSixteen/keyboard.sch

## KiCad design keyboard.sch (2025-10-18)

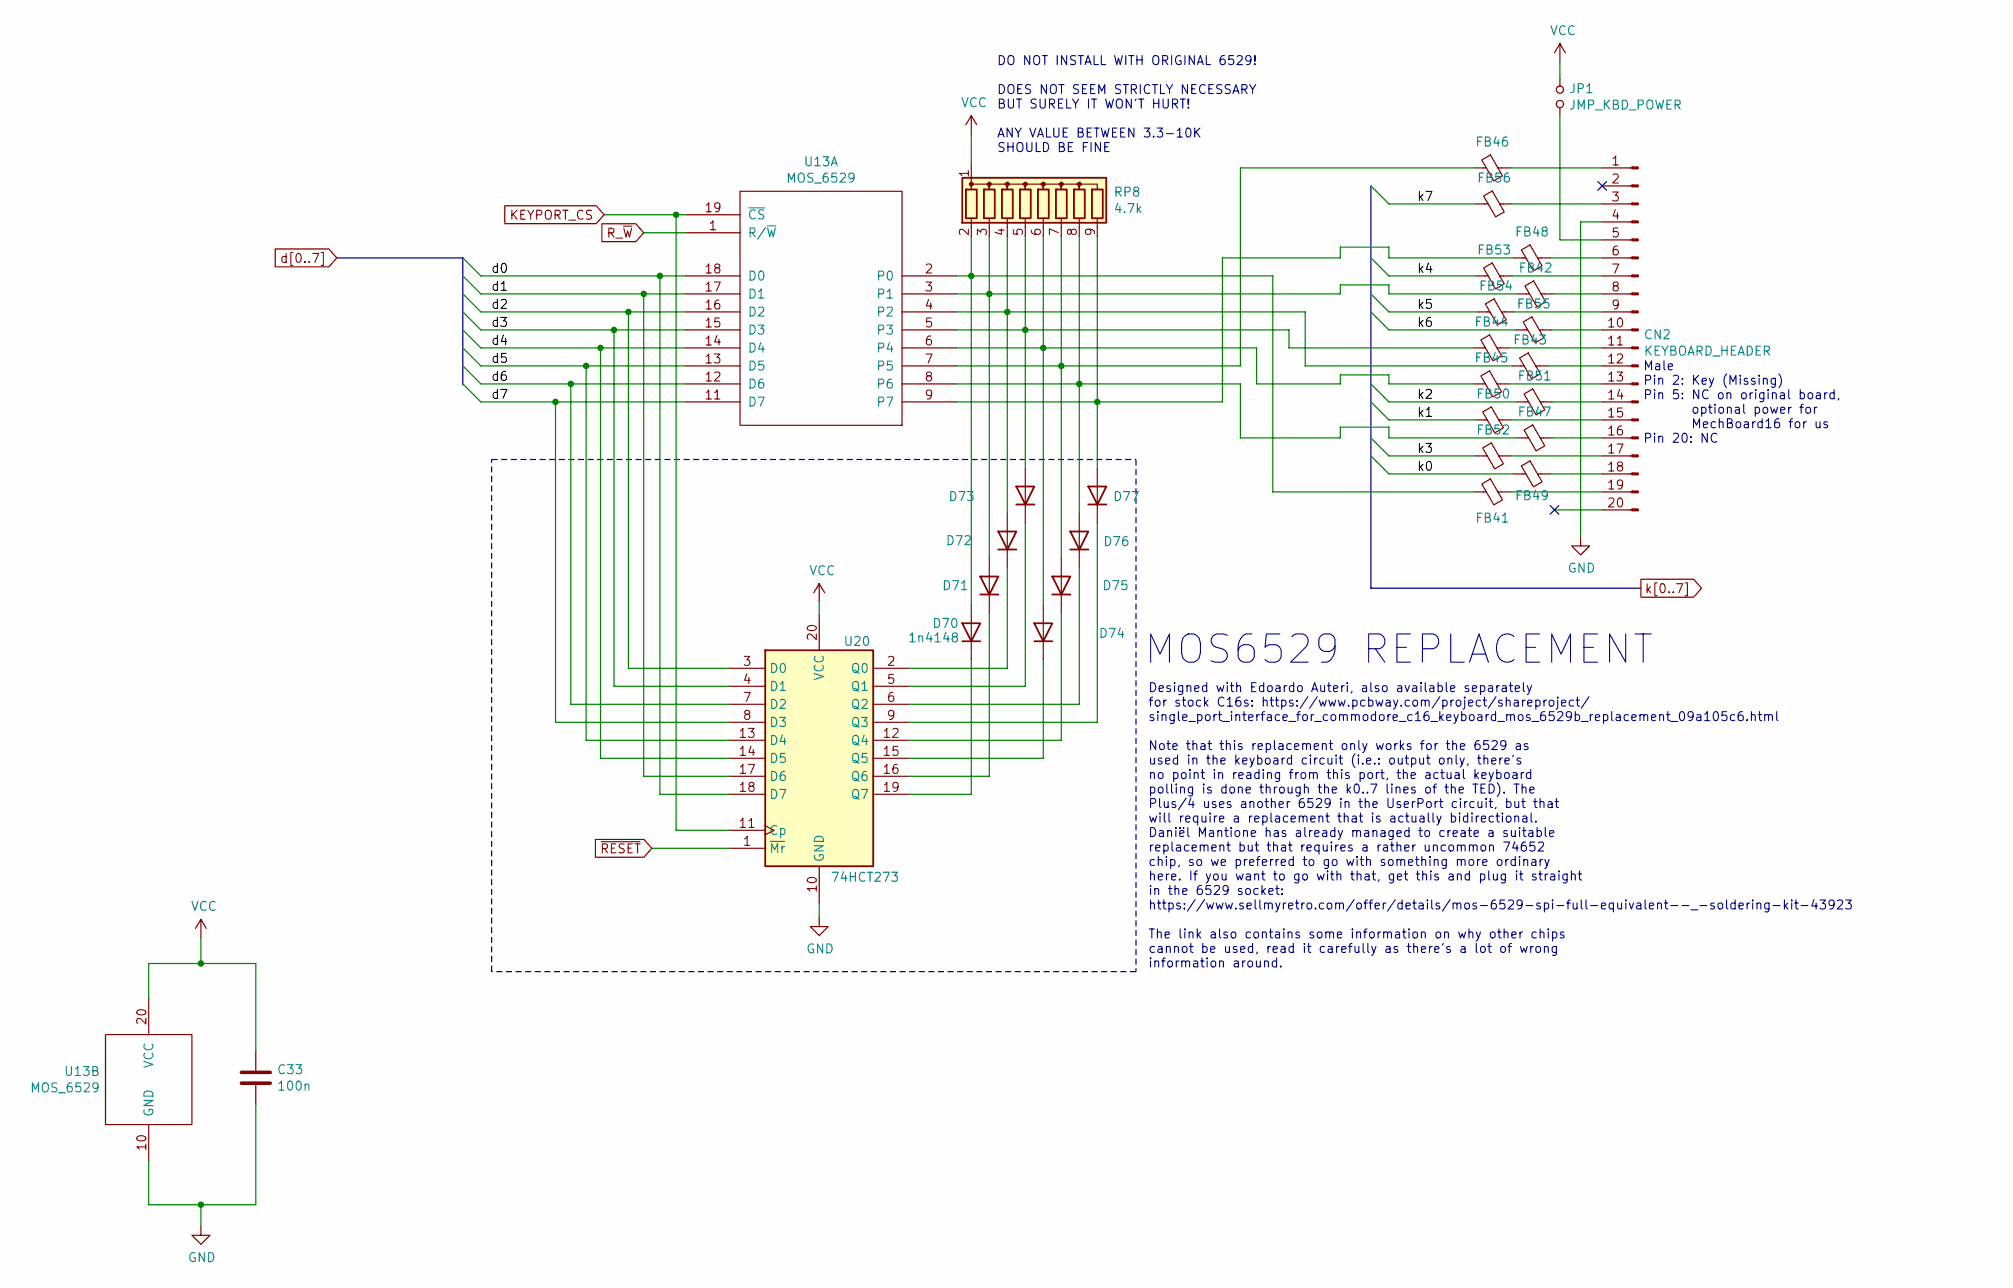
[picture p37: schematic keyboard.sch]

Parts:
C33: 100n; C_Disc_D8.0mm_W2.5mm_P5.00mm; MouserPN 810-FG28X7R1H104KNT0
CN2: KEYBOARD_HEADER; PinHeader_1x20_P2.54mm_NoPin2
D70, D71, D72, D73, D74, D75, D76, D77: 1n4148; D_DO-35_SOD27_P5.08mm_Vertical_KathodeUp
FB41, FB42, FB43, FB44, FB45, FB46, FB47, FB48, FB49, FB50, FB51, FB52, FB53, FB54, FB55, FB56: FERRITE; EMI_Filter; MouserPN 623-2743015112
JP1: JMP_KBD_POWER; SolderJumper-2_P1.3mm_Open_RoundedPad1.0x1.5mm; MouserPN ---
RP8: 4.7k; R_Array_SIP9
U13: MOS_6529; DIP-20_W7.62mm_Socket_LongPads; MouserPN :)
U20: 74HCT273; DIP-20_W7.62mm_Socket_LongPads; MouserPN 595-CD74HCT273E

Connections:
GND: C33.2, CN2.4, U13.10 (GND), U20.10 (GND)
KEYPORT_CS: U13.19 (~CS), U20.11 (Cp)
unnamed: CN2.1, FB46.2
unnamed: CN2.3, FB56.2
unnamed: CN2.5, JP1.2
unnamed: CN2.6, FB48.2
unnamed: CN2.7, FB53.2
unnamed: CN2.8, FB42.2
unnamed: CN2.9, FB54.2
unnamed: CN2.10, FB55.2
unnamed: CN2.11, FB44.2
unnamed: CN2.12, FB43.2
unnamed: CN2.13, FB45.2
unnamed: CN2.14, FB51.2
unnamed: CN2.15, FB50.2
unnamed: CN2.16, FB47.2
unnamed: CN2.17, FB52.2
unnamed: CN2.18, FB49.2
unnamed: CN2.19, FB41.2
unnamed: D70.1 (K), U20.19 (Q7)
unnamed: D70.2 (A), FB41.1, RP8.2 (R1), U13.2 (P0)
unnamed: D71.1 (K), U20.16 (Q6)
unnamed: D71.2 (A), FB42.1, RP8.3 (R2), U13.3 (P1)
unnamed: D72.1 (K), U20.2 (Q0)
unnamed: D72.2 (A), FB43.1, RP8.4 (R3), U13.4 (P2)
unnamed: D73.1 (K), U20.5 (Q1)
unnamed: D73.2 (A), FB44.1, RP8.5 (R4), U13.5 (P3)
unnamed: D74.1 (K), U20.15 (Q5)
unnamed: D74.2 (A), FB45.1, RP8.6 (R5), U13.6 (P4)
unnamed: D75.1 (K), U20.12 (Q4)
unnamed: D75.2 (A), FB46.1, RP8.7 (R6), U13.7 (P5)
unnamed: D76.1 (K), U20.6 (Q2)
unnamed: D76.2 (A), FB47.1, RP8.8 (R7), U13.8 (P6)
unnamed: D77.1 (K), U20.9 (Q3)
unnamed: D77.2 (A), FB48.1, RP8.9 (R8), U13.9 (P7)
R_~W: U13.1 (R/~W)
VCC: C33.1, JP1.1, RP8.1 (common), U13.20 (VCC), U20.20 (VCC)
d0: U13.18 (D0), U20.18 (D7)
d1: U13.17 (D1), U20.17 (D6)
d2: U13.16 (D2), U20.3 (D0)
d3: U13.15 (D3), U20.4 (D1)
d4: U13.14 (D4), U20.14 (D5)
d5: U13.13 (D5), U20.13 (D4)
d6: U13.12 (D6), U20.7 (D2)
d7: U13.11 (D7), U20.8 (D3)
k0: FB49.1
k1: FB50.1
k2: FB51.1
k3: FB52.1
k4: FB53.1
k5: FB54.1
k6: FB55.1
k7: FB56.1
~RESET: U20.1 (~Mr)

Notes on the sheet:
Male Pin 2: Key (Missing) Pin 5: NC on original board, optional power for MechBoard16 for us Pin 20: NC
Designed with Edoardo Auteri, also available separately for stock C16s: https://www.pcbway.com/project/shareproject/ single_port_interface_for_commodore_c16_keyboard_mos_6529b_replacement_09a105c6.html Note that this replacement only works for the 6529 as used in the keyboard circuit (i.e.: output 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
MOS6529 REPLACEMENT
DO NOT INSTALL WITH ORIGINAL 6529! DOES NOT SEEM STRICTLY NECESSARY BUT SURELY IT WON'T HURT! ANY VALUE BETWEEN 3.3-10K SHOULD BE FINE
