SukkoPera/LittleSixteen/misc.sch

## KiCad design misc.sch (2025-10-18)

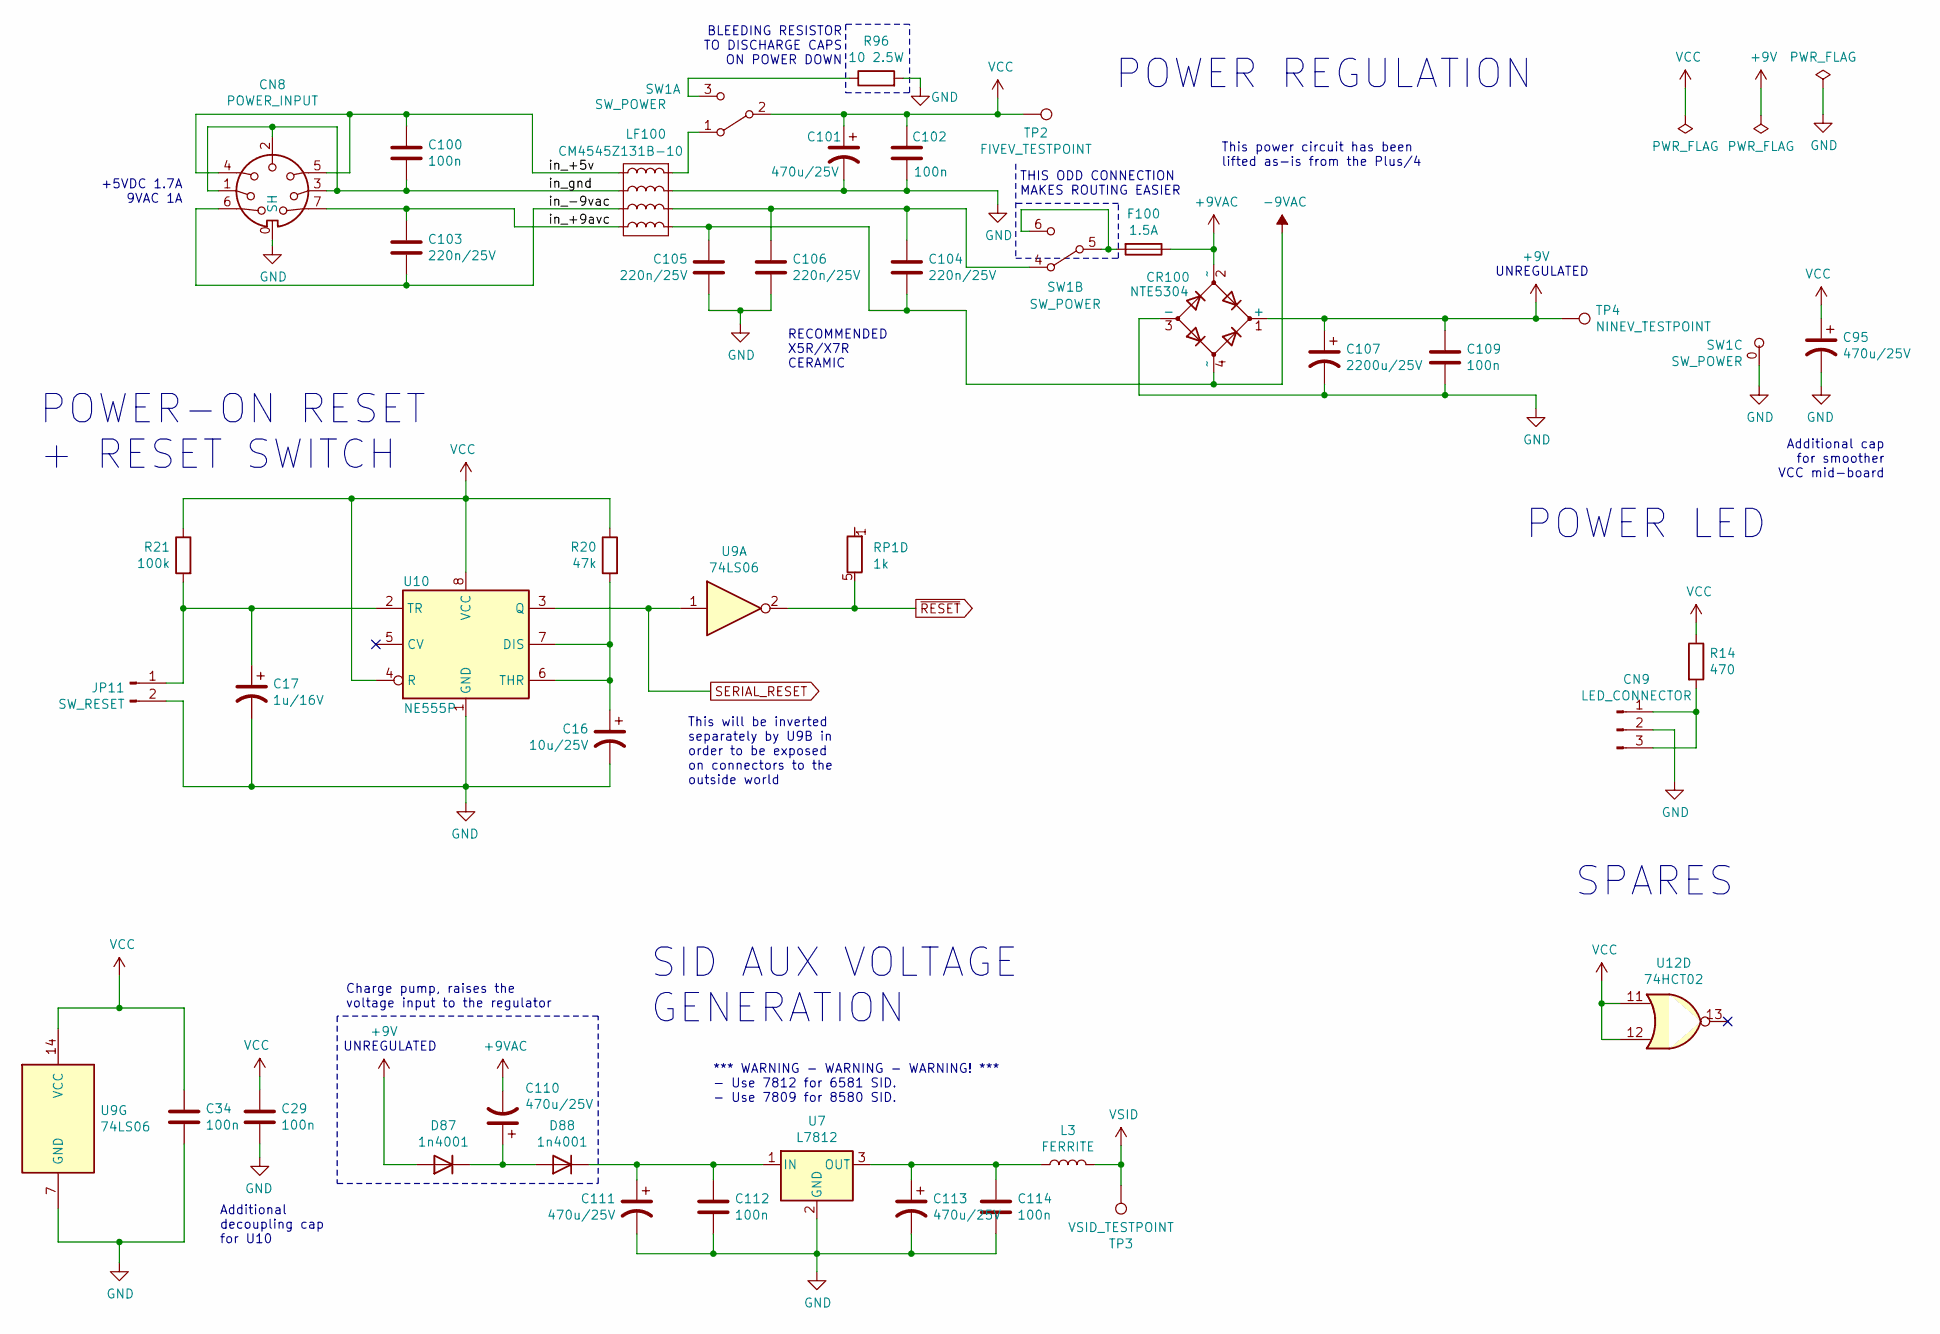
[picture p38: schematic misc.sch]

Parts:
C16: 10u/25V; CP_Radial_D5.0mm_P2.00mm; MouserPN 710-860010572002
C17: 1u/16V; CP_Radial_D5.0mm_P2.00mm; MouserPN 710-860010672005
C29, C34, C100, C102, C109, C112, C114: 100n; C_Disc_D8.0mm_W2.5mm_P5.00mm; MouserPN 810-FG28X7R1H104KNT0
C95, C101, C110, C111, C113: 470u/25V; CP_Radial_D8.0mm_P3.50mm; MouserPN 710-860010474013
C103, C104, C105, C106: 220n/25V; C_Disc_D8.0mm_W2.5mm_P5.00mm
C107: 2200u/25V; Axial_Cap_Dual
CN8: POWER_INPUT; DIN-7_DS_7_102_OR_102B
CN9: LED_CONNECTOR; PinHeader_1x03_P2.54mm_Vertical
CR100: NTE5304; Diode_Bridge_Round_D9.8mm
D87, D88: 1n4001; D_DO-41_SOD81_P5.08mm_Vertical_KathodeUp
F100: 1.5A; Fuseholder_Cylinder-5x20mm_Stelvio-Kontek_PTF78_Horizontal_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; MouserPN 504-BK1/GMA-1.5-R + 693-0031.8201
JP11: SW_RESET; PinHeader_1x02_P2.54mm_Vertical
L3: FERRITE; L_Radial_D6.0mm_P4.00mm; MouserPN 875-28C0236-0EW-10
LF100: CM4545Z131B-10; MouserPN 875-CM4545Z131B-10
R14: 470; R_Axial_DIN0207_L6.3mm_D2.5mm_P5.08mm_Vertical
R20: 47k; R_Axial_DIN0207_L6.3mm_D2.5mm_P5.08mm_Vertical
R21: 100k; R_Axial_DIN0207_L6.3mm_D2.5mm_P5.08mm_Vertical; MouserPN 603-MFR-25FBF52-100K
R96: 10 2.5W; R_Axial_DIN0414_L11.9mm_D4.5mm_P5.08mm_Vertical
RP1: 1k; R_Array_SIP6
SW1: SW_POWER; C64_PowerSwitch
TP2: FIVEV_TESTPOINT; TestPoint_Pad_D2.0mm; MouserPN ---
TP3: VSID_TESTPOINT; TestPoint_Pad_D2.0mm; MouserPN ---
TP4: NINEV_TESTPOINT; TestPoint_Pad_D2.0mm; MouserPN ---
U7: L7812; TO-220-3_Vertical
U9: 74LS06; DIP-14_W7.62mm_Socket_LongPads
U10: NE555P; DIP-8_W7.62mm_Socket_LongPads
U12: 74HCT02; DIP-14_W7.62mm_Socket_LongPads; MouserPN 595-SN74HCT02N

Connections:
+9V: C107.1, C109.1, CR100.1 (+), D87.2 (A), TP4.1
+9VAC: C110.2, CR100.2 (~~), F100.1
-9VAC: C104.2, C105.1, CR100.4 (~~), LF100.4
GND: C16.2, C17.2, C29.2, C34.2, C95.2, C101.2, C102.2, C105.2, C106.2, C107.2, C109.2, C111.2, C112.2, C113.2, C114.2, CN8.0 (SH), CN9.2, CR100.3 (-), JP11.2, LF100.2, R96.2, SW1.0 (SH), U7.2 (GND), U9.7 (GND), U10.1 (GND)
unnamed: C16.1, R20.2, U10.6 (THR), U10.7 (DIS)
unnamed: C17.1, JP11.1, R21.2, U10.2 (TR)
unnamed: C104.1, C106.1, LF100.3, SW1.4 (A)
unnamed: C110.1, D87.1 (K), D88.2 (A)
unnamed: C111.1, C112.1, D88.1 (K), U7.1 (IN)
unnamed: C113.1, C114.1, L3.1, U7.3 (OUT)
unnamed: CN9.1, CN9.3, R14.2
unnamed: F100.2, SW1.5 (B), SW1.6 (C)
unnamed: LF100.1, SW1.1 (A)
unnamed: R96.1, SW1.3 (C)
SERIAL_RESET: U9.1, U10.3 (Q)
VCC: C29.1, C34.1, C95.1, C101.1, C102.1, R14.1, R20.1, R21.1, SW1.2 (B), TP2.1, U9.14 (VCC), U10.4 (R), U10.8 (VCC), U12.11, U12.12
VSID: L3.2, TP3.1
in_+5v: C100.1, CN8.4, CN8.5, LF100.8
in_+9avc: C103.1, CN8.7, LF100.5
in_-9vac: C103.2, CN8.6, LF100.6
in_gnd: C100.2, CN8.1, CN8.2, CN8.3, LF100.7
~RESET: RP1.5 (R4.2), U9.2

Notes on the sheet:
POWER LED
SPARES
POWER-ON RESET + RESET SWITCH
Additional decoupling cap for U10
This will be inverted separately by U9B in order to be exposed on connectors to the outside world
POWER REGULATION
RECOMMENDED X5R/X7R CERAMIC
UNREGULATED
This power circuit has been lifted as-is from the Plus/4
+5VDC 1.7A 9VAC 1A
Additional cap for smoother VCC mid-board
BLEEDING RESISTOR TO DISCHARGE CAPS ON POWER DOWN
THIS ODD CONNECTION MAKES ROUTING EASIER
*** WARNING - WARNING - WARNING! *** - Use 7812 for 6581 SID. - Use 7809 for 8580 SID.
SID AUX VOLTAGE GENERATION
Charge pump, raises the voltage input to the regulator
