SukkoPera/LittleSixteen/pla.sch

## KiCad design pla.sch (2025-10-18)

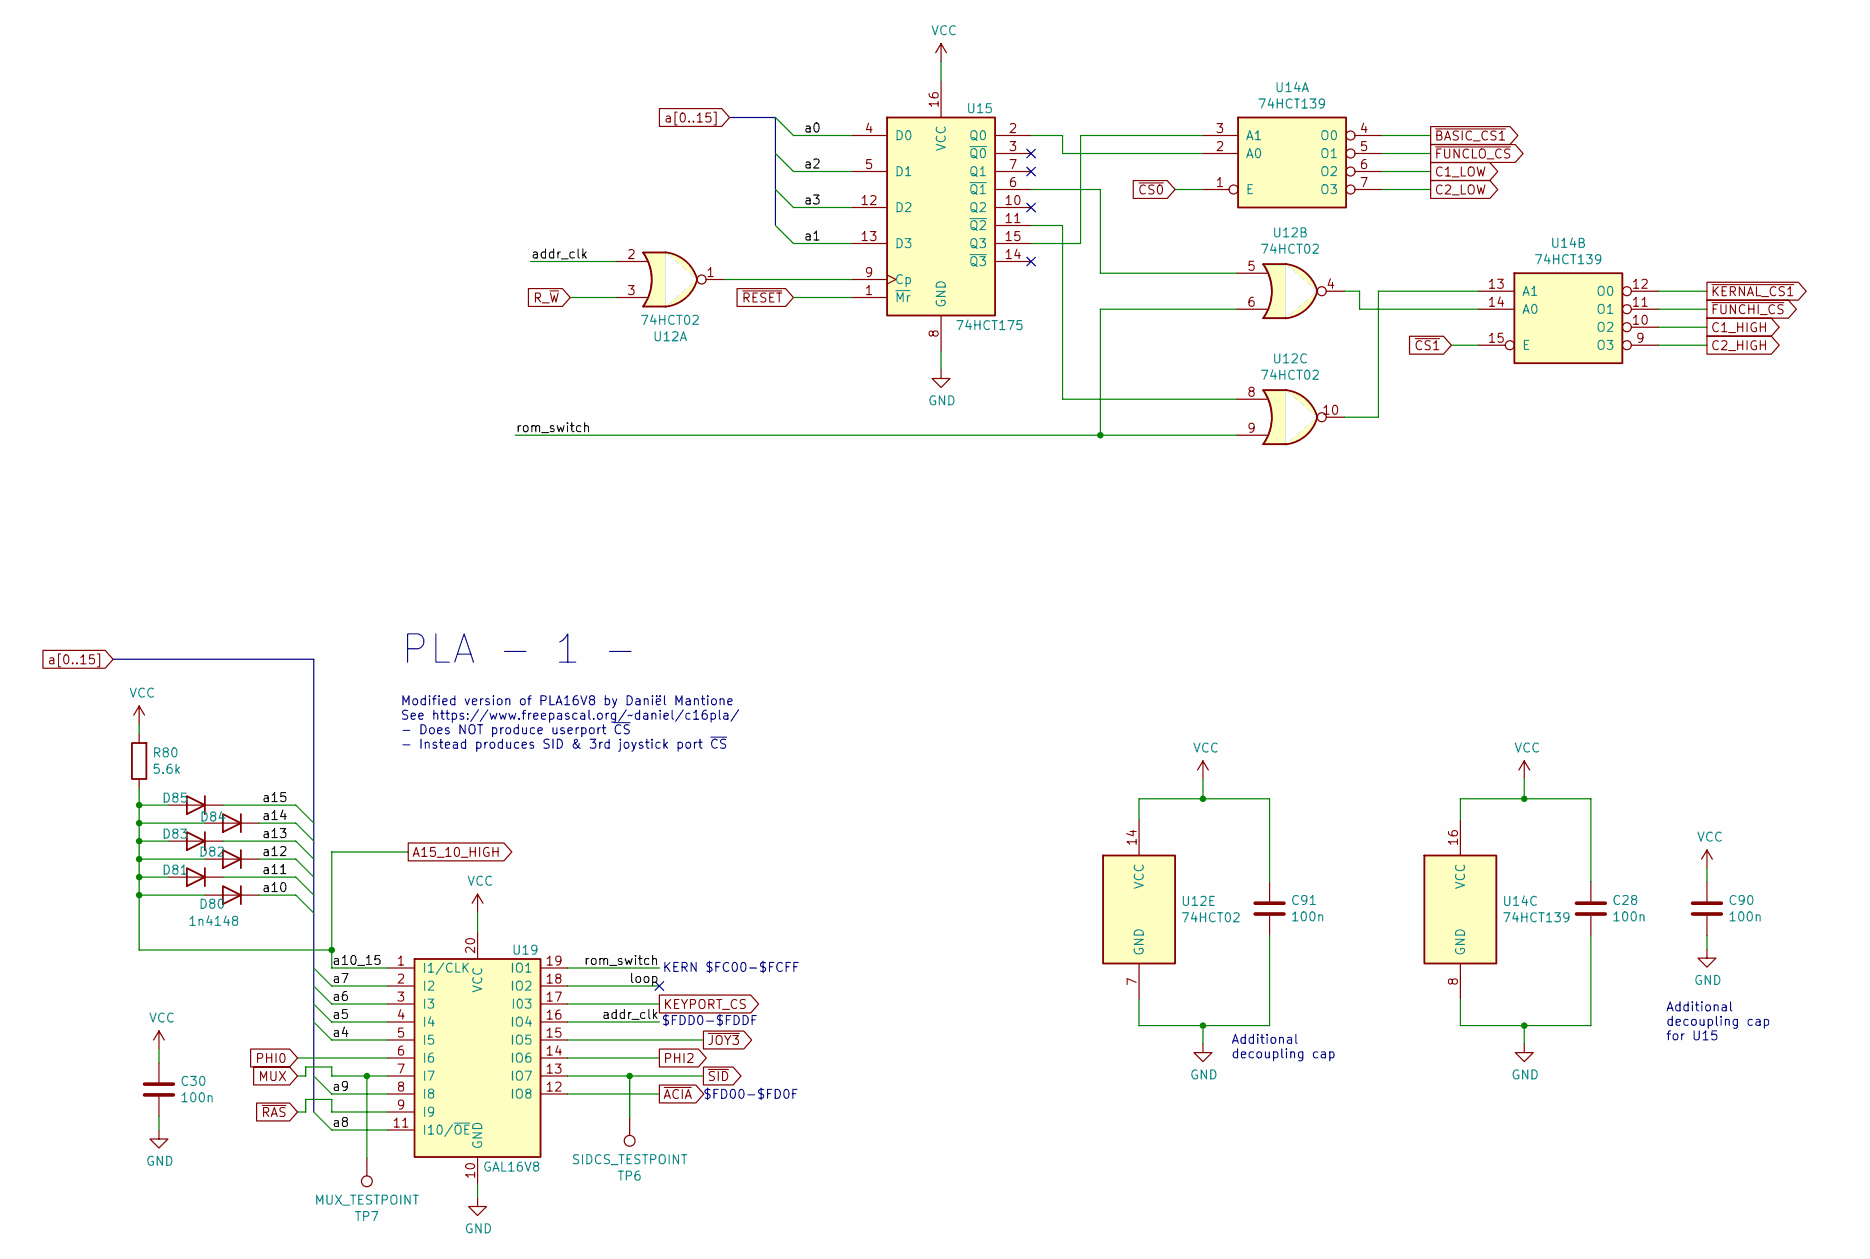
[picture p39: schematic pla.sch]

Parts:
C28, C30, C90, C91: 100n; C_Disc_D8.0mm_W2.5mm_P5.00mm; MouserPN 810-FG28X7R1H104KNT0
D80, D81, D82, D83, D84, D85: 1n4148; D_DO-35_SOD27_P5.08mm_Vertical_KathodeUp
R80: 5.6k; R_Axial_DIN0207_L6.3mm_D2.5mm_P5.08mm_Vertical
TP6: SIDCS_TESTPOINT; TestPoint_Pad_D2.0mm; MouserPN ---
TP7: MUX_TESTPOINT; TestPoint_Pad_D2.0mm; MouserPN ---
U12: 74HCT02; DIP-14_W7.62mm_Socket_LongPads; MouserPN 595-SN74HCT02N
U14: 74HCT139; DIP-16_W7.62mm_Socket_LongPads; MouserPN 595-SN74HCT139N
U15: 74HCT175; DIP-16_W7.62mm_Socket_LongPads; MouserPN 595-CD74HCT175E
U19: GAL16V8; DIP-20_W7.62mm_Socket_LongPads; MouserPN 556-AF16V8B15PU

Connections:
A15_10_HIGH: D80.2 (A), D81.2 (A), D82.2 (A), D83.2 (A), D84.2 (A), D85.2 (A), R80.1, U19.1 (I1/CLK)
C1_HIGH: U14.10 (O2)
C1_LOW: U14.6 (O2)
C2_HIGH: U14.9 (O3)
C2_LOW: U14.7 (O3)
GND: C28.2, C30.2, C90.2, C91.2, U12.7 (GND), U14.8 (GND), U15.8 (GND), U19.10 (GND)
KEYPORT_CS: U19.17 (I03)
MUX: TP7.1, U19.7 (I7)
unnamed: U12.1, U15.9 (Cp)
unnamed: U12.4, U14.14 (A0)
unnamed: U12.5, U15.6 (~Q1)
unnamed: U12.8, U15.11 (~Q2)
unnamed: U12.10, U14.13 (A1)
unnamed: U14.2 (A0), U15.2 (Q0)
unnamed: U14.3 (A1), U15.15 (Q3)
PHI0: U19.6 (I6)
PHI2: U19.14 (IO6)
R_~W: U12.3
VCC: C28.1, C30.1, C90.1, C91.1, R80.2, U12.14 (VCC), U14.16 (VCC), U15.16 (VCC), U19.20 (VCC)
a0: U15.4 (D0)
a1: U15.13 (D3)
a2: U15.5 (D1)
a3: U15.12 (D2)
a4: U19.5 (I5)
a5: U19.4 (I4)
a6: U19.3 (I3)
a7: U19.2 (I2)
a8: U19.11 (I10/~OE~)
a9: U19.8 (I8)
a10: D80.1 (K)
a11: D81.1 (K)
a12: D82.1 (K)
a13: D83.1 (K)
a14: D84.1 (K)
a15: D85.1 (K)
addr_clk: U12.2, U19.16 (IO4)
loop: U19.18 (IO2)
rom_switch: U12.6, U12.9, U19.19 (IO1)
~ACIA: U19.12 (IO8)
~BASIC_CS1: U14.4 (O0)
~CS0: U14.1 (E)
~CS1: U14.15 (E)
~FUNCHI_CS: U14.11 (O1)
~FUNCLO_CS: U14.5 (O1)
~JOY3: U19.15 (IO5)
~KERNAL_CS1: U14.12 (O0)
~RAS: U19.9 (I9)
~RESET: U15.1 (~Mr)
~SID: TP6.1, U19.13 (IO7)

Notes on the sheet:
Additional decoupling cap
Additional decoupling cap for U15
PLA - 1 -
Modified version of PLA16V8 by Daniël Mantione See https://www.freepascal.org/~~daniel/c16pla/ - Does NOT produce userport ~CS~ - Instead produces SID & 3rd joystick port ~CS~
$FD00-$FD0F
$FDD0-$FDDF
KERN $FC00-$FCFF
