SukkoPera/LittleSixteen/ram.sch

## KiCad design ram.sch (2025-10-18)

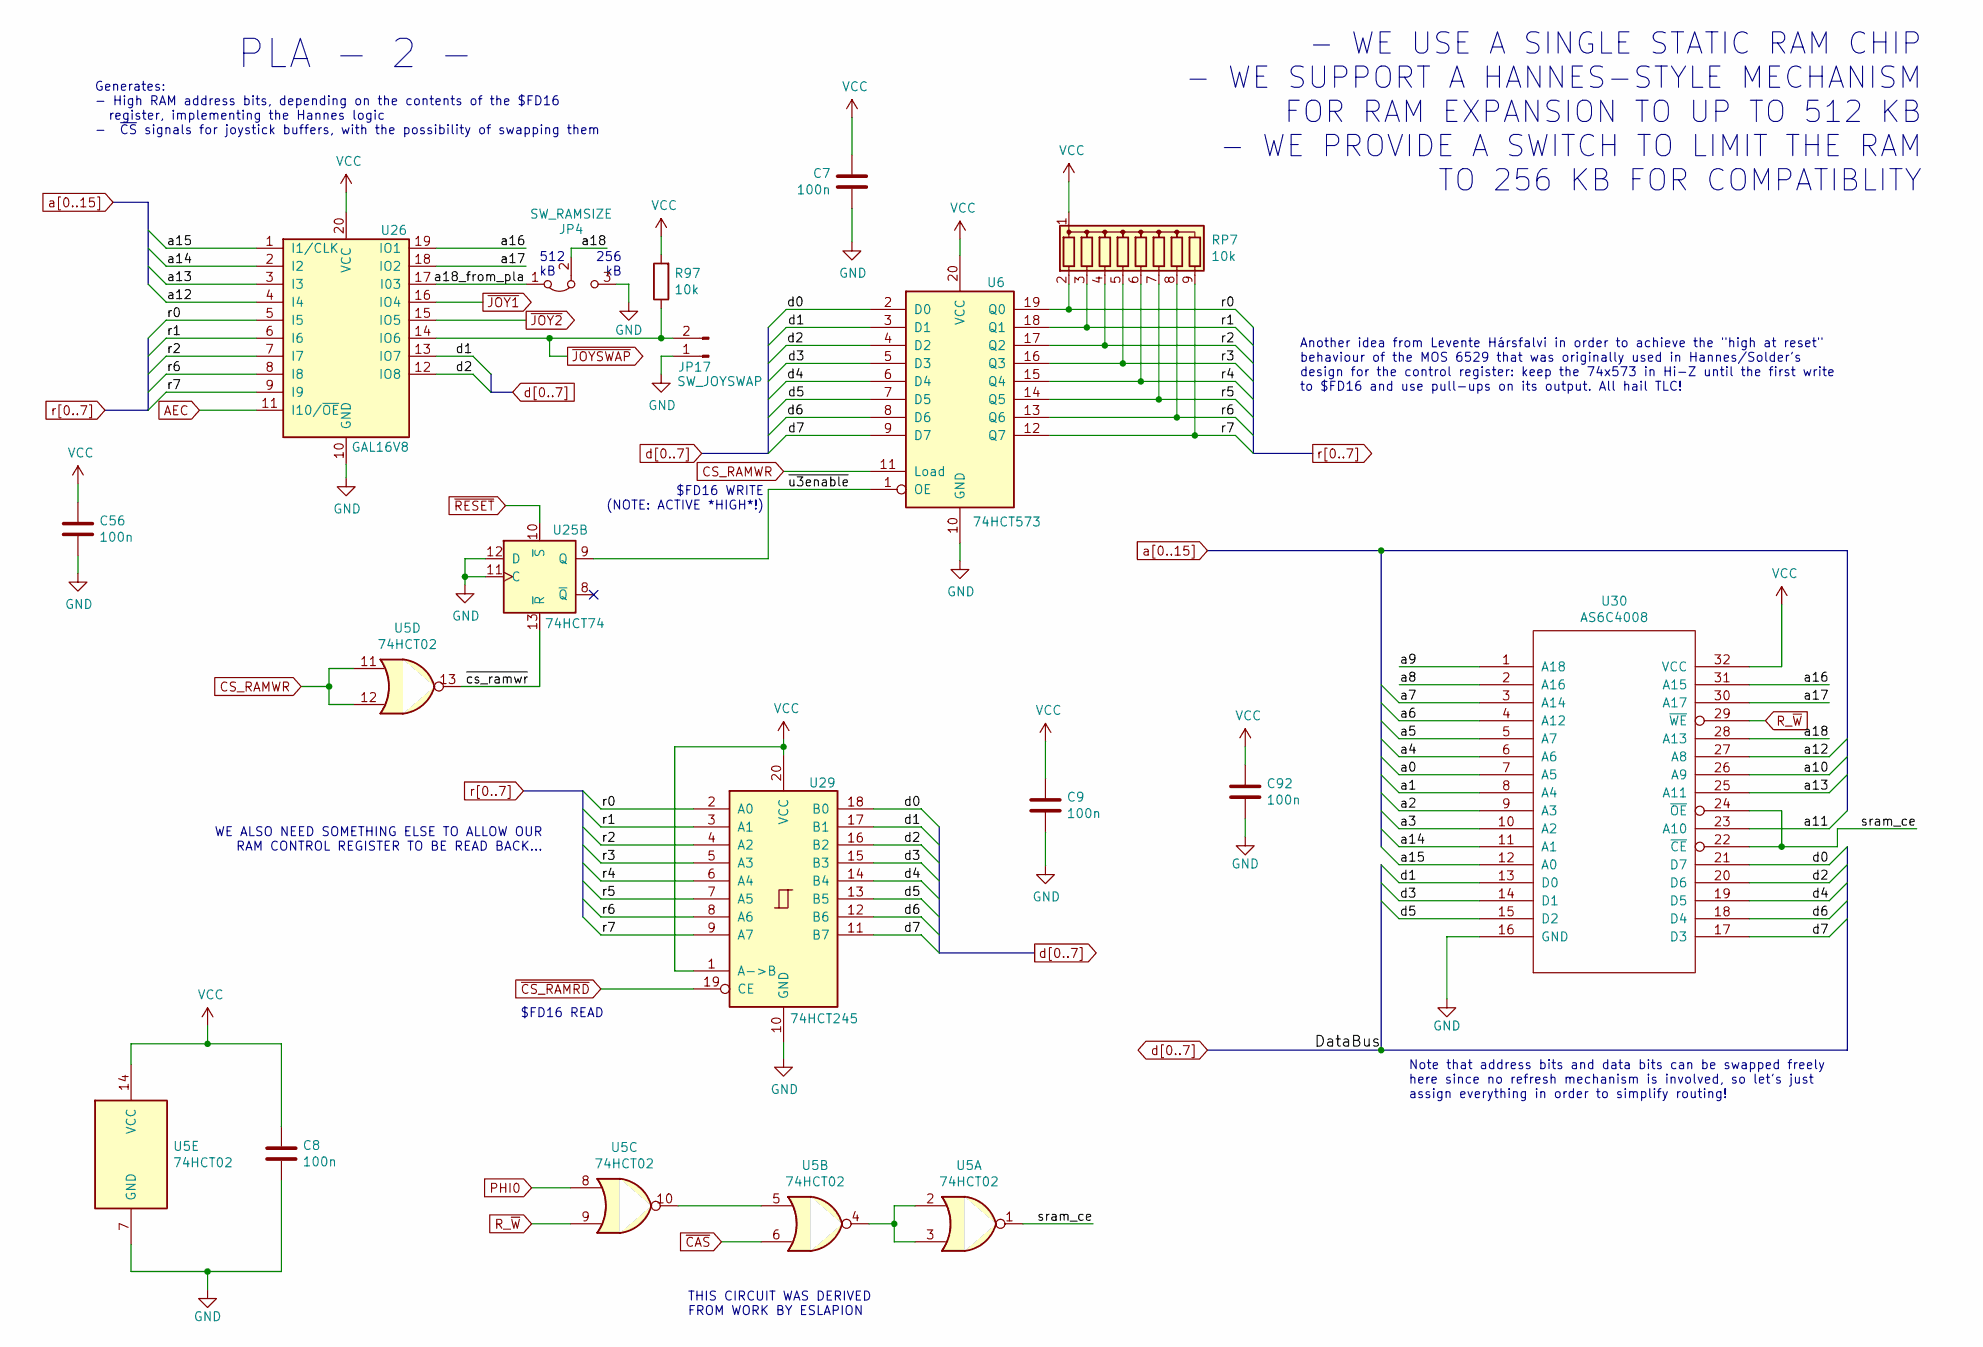
[picture p40: schematic ram.sch]

Parts:
C7, C8, C9, C56, C92: 100n; C_Disc_D8.0mm_W2.5mm_P5.00mm; MouserPN 810-FG28X7R1H104KNT0
JP4: SW_RAMSIZE; PinHeader_1x03_P2.54mm_Vertical; MouserPN ---
JP17: SW_JOYSWAP; PinHeader_1x02_P2.54mm_Vertical
R97: 10k; R_Axial_DIN0207_L6.3mm_D2.5mm_P5.08mm_Vertical; MouserPN 603-MFR-25FTF52-10K
RP7: 10k; R_Array_SIP9
U5: 74HCT02; DIP-14_W7.62mm_Socket_LongPads; MouserPN 595-SN74HCT02N
U6: 74HCT573; DIP-20_W7.62mm_Socket_LongPads; MouserPN 595-SN74HCT573NSR
U25: 74HCT74; DIP-14_W7.62mm_Socket_LongPads; MouserPN 595-SN74HC74N
U26: GAL16V8; DIP-20_W7.62mm_Socket_LongPads; MouserPN 556-AF16V8B15PU
U29: 74HCT245; DIP-20_W7.62mm_Socket_LongPads; MouserPN 595-SN74HCT245N
U30: AS6C4008; DIP-32_W15.24mm_Socket_LongPads; MouserPN 913-AS6C4008-55PIN

Connections:
AEC: U26.11 (I10/~OE~)
CS_RAMWR: U5.11, U5.12, U6.11 (Load)
GND: C7.2, C8.2, C9.1, C56.2, C92.2, JP4.3 (B), JP17.1, U5.7 (GND), U6.10 (GND), U25.11 (C), U25.12 (D), U26.10 (GND), U29.10 (GND), U30.16 (GND)
unnamed: U5.2, U5.3, U5.4
unnamed: U5.5, U5.10
PHI0: U5.8
R_~W: U5.9, U30.29 (~WE)
VCC: C7.1, C8.1, C9.2, C56.1, C92.1, R97.2, RP7.1 (common), U5.14 (VCC), U6.20 (VCC), U26.20 (VCC), U29.1 (A->B), U29.20 (VCC), U30.32 (VCC)
a0: U30.7 (A5)
a1: U30.8 (A4)
a2: U30.9 (A3)
a3: U30.10 (A2)
a4: U30.6 (A6)
a5: U30.5 (A7)
a6: U30.4 (A12)
a7: U30.3 (A14)
a8: U30.2 (A16)
a9: U30.1 (A18)
a10: U30.26 (A9)
a11: U30.23 (A10)
a12: U26.4 (I4), U30.27 (A8)
a13: U26.3 (I3), U30.25 (A11)
a14: U26.2 (I2), U30.11 (A1)
a15: U26.1 (I1/CLK), U30.12 (A0)
a16: U26.19 (IO1), U30.31 (A15)
a17: U26.18 (IO2), U30.30 (A17)
a18: JP4.2 (C), U30.28 (A13)
a18_from_pla: JP4.1 (A), U26.17 (I03)
d0: U6.2 (D0), U29.18 (B0), U30.21 (D7)
d1: U6.3 (D1), U26.13 (IO7), U29.17 (B1), U30.13 (D0)
d2: U6.4 (D2), U26.12 (IO8), U29.16 (B2), U30.20 (D6)
d3: U6.5 (D3), U29.15 (B3), U30.14 (D1)
d4: U6.6 (D4), U29.14 (B4), U30.19 (D5)
d5: U6.7 (D5), U29.13 (B5), U30.15 (D2)
d6: U6.8 (D6), U29.12 (B6), U30.18 (D4)
d7: U6.9 (D7), U29.11 (B7), U30.17 (D3)
r0: RP7.2 (R1), U6.19 (Q0), U26.5 (I5), U29.2 (A0)
r1: RP7.3 (R2), U6.18 (Q1), U26.6 (I6), U29.3 (A1)
r2: RP7.4 (R3), U6.17 (Q2), U26.7 (I7), U29.4 (A2)
r3: RP7.5 (R4), U6.16 (Q3), U29.5 (A3)
r4: RP7.6 (R5), U6.15 (Q4), U29.6 (A4)
r5: RP7.7 (R6), U6.14 (Q5), U29.7 (A5)
r6: RP7.8 (R7), U6.13 (Q6), U26.8 (I8), U29.8 (A6)
r7: RP7.9 (R8), U6.12 (Q7), U26.9 (I9), U29.9 (A7)
sram_ce: U5.1, U30.22 (~CE), U30.24 (~OE)
~CAS: U5.6
~CS_RAMRD: U29.19 (CE)
~JOY1: U26.16 (IO4)
~JOY2: U26.15 (IO5)
~JOYSWAP: JP17.2, R97.1, U26.14 (IO6)
~RESET: U25.10 (~S)
~cs_ramwr: U5.13, U25.13 (~R)
~u3enable: U6.1 (OE), U25.9 (Q)

Notes on the sheet:
THIS CIRCUIT WAS DERIVED FROM WORK BY ESLAPION
$FD16 READ
WE ALSO NEED SOMETHING ELSE TO ALLOW OUR RAM CONTROL REGISTER TO BE READ BACK...
PLA - 2 -
$FD16 WRITE (NOTE: ACTIVE *HIGH*!)
Generates: - High RAM address bits, depending on the contents of the $FD16 register, implementing the Hannes logic - ~CS~ signals for joystick buffers, with the possibility of swapping them
Note that address bits and data bits can be swapped freely here since no refresh mechanism is involved, so let's just assign everything in order to simplify routing!
Another idea from Levente Hársfalvi in order to achieve the "high at reset" behaviour of the MOS 6529 that was originally used in Hannes/Solder's design for the control register: keep the 74x573 in Hi-Z until the first write to $FD16 and use pull-ups on its output. All hail TLC!
- WE USE A SINGLE STATIC RAM CHIP - WE SUPPORT A HANNES-STYLE MECHANISM FOR RAM EXPANSION TO UP TO 512 KB - WE PROVIDE A SWITCH TO LIMIT THE RAM TO 256 KB FOR COMPATIBLITY
512 kB
256 kB
