SukkoPera/LittleSixteen/rom.sch

## KiCad design rom.sch (2025-10-18)

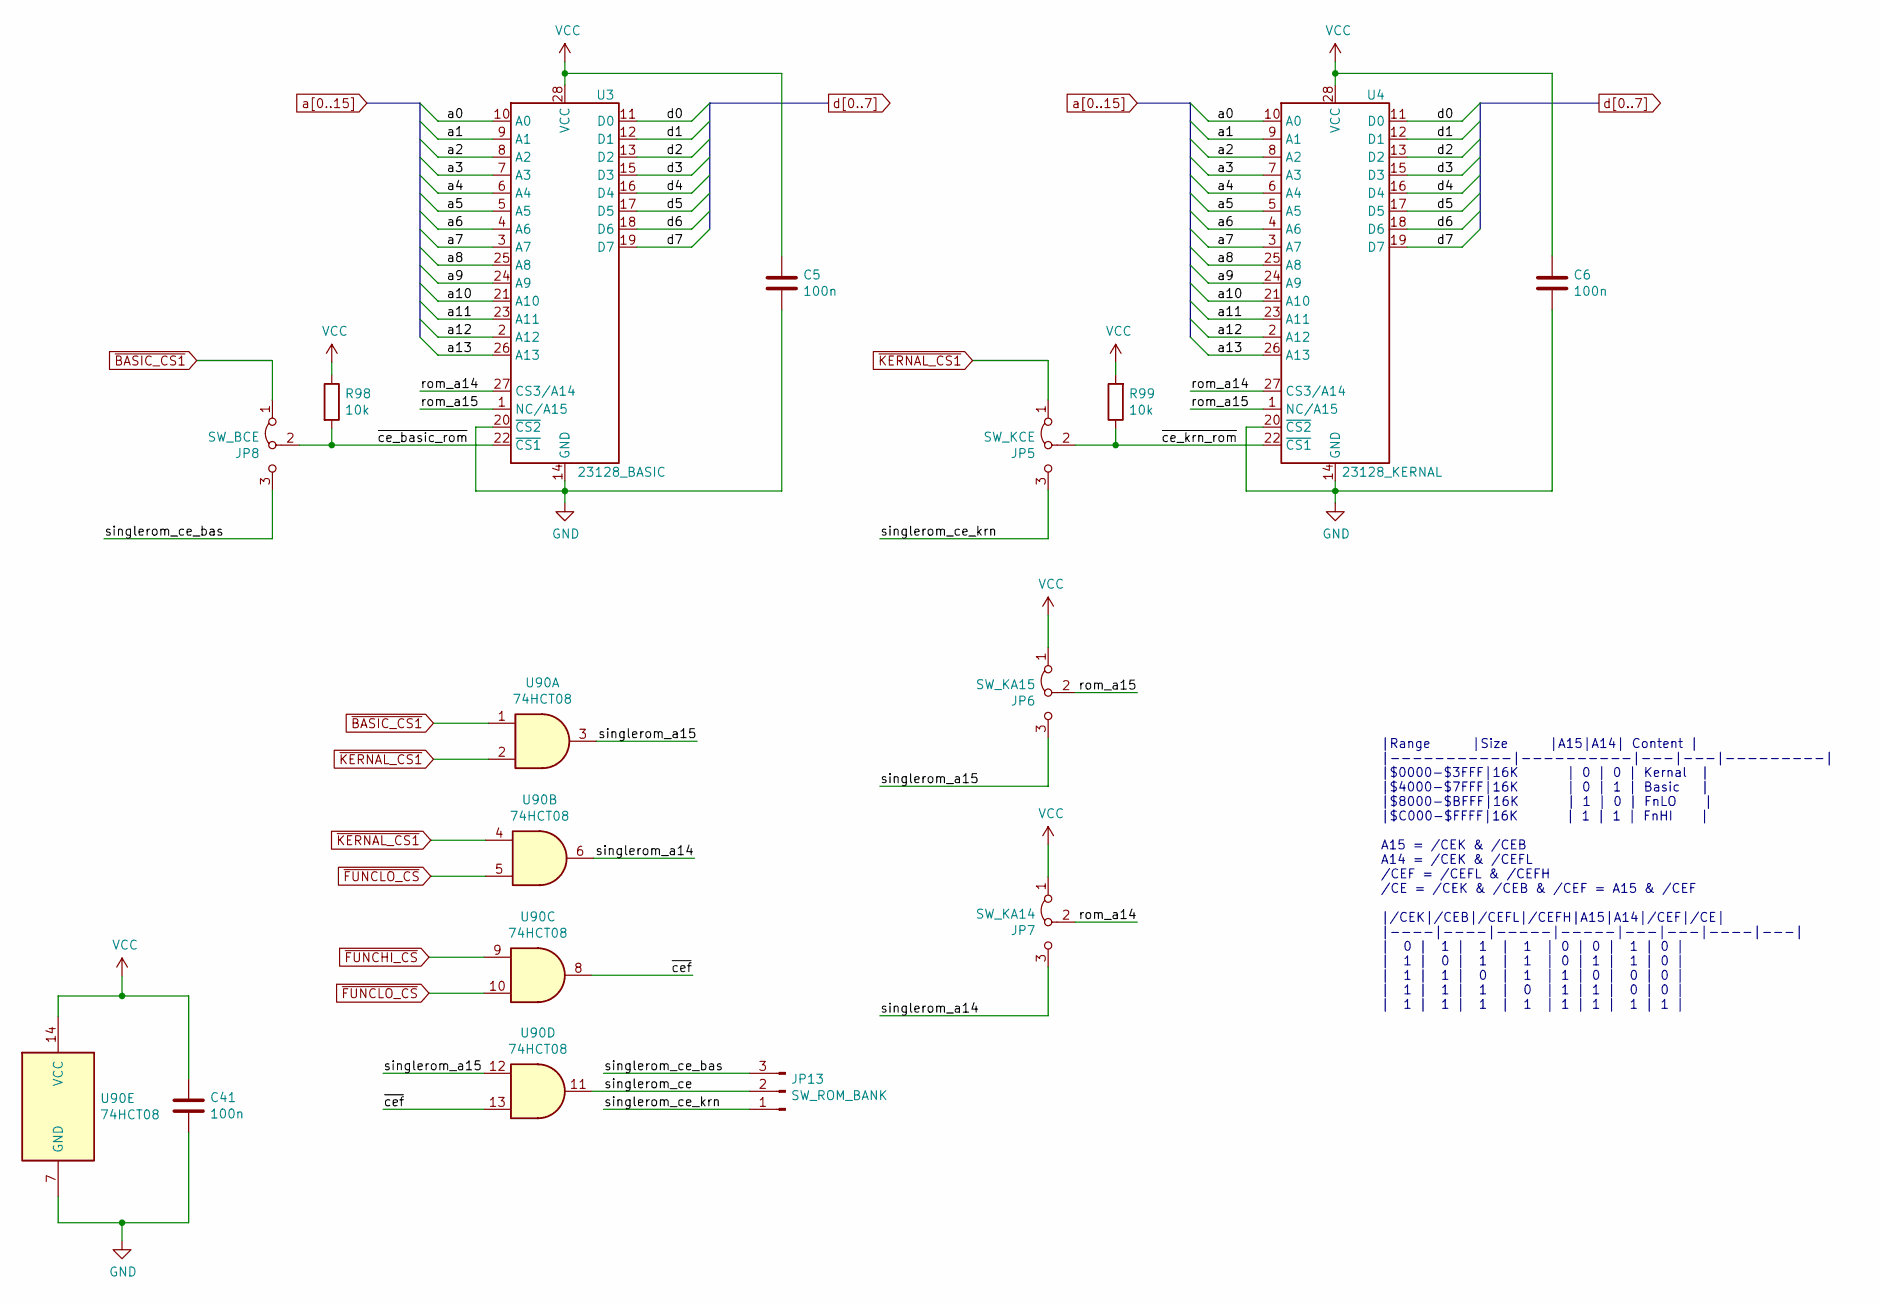
[picture p41: schematic rom.sch]

Parts:
C5, C6, C41: 100n; C_Disc_D8.0mm_W2.5mm_P5.00mm; MouserPN 810-FG28X7R1H104KNT0
JP5: SW_KCE; SolderJumper-3_P1.3mm_Open_RoundedPad1.0x1.5mm; MouserPN ---
JP6: SW_KA15; SolderJumper-3_P1.3mm_Open_RoundedPad1.0x1.5mm; MouserPN ---
JP7: SW_KA14; SolderJumper-3_P1.3mm_Open_RoundedPad1.0x1.5mm; MouserPN ---
JP8: SW_BCE; SolderJumper-3_P1.3mm_Open_RoundedPad1.0x1.5mm; MouserPN ---
JP13: SW_ROM_BANK; PinHeader_1x03_P2.54mm_Vertical
R98, R99: 10k; R_Axial_DIN0207_L6.3mm_D2.5mm_P5.08mm_Vertical; MouserPN 603-MFR-25FTF52-10K
U3: 23128_BASIC; DIP-28_W15.24mm_Socket_LongPads; MouserPN :)
U4: 23128_KERNAL; DIP-28_W15.24mm_Socket_LongPads; MouserPN :)
U90: 74HCT08; DIP-14_W7.62mm_Socket_LongPads; MouserPN 595-SN74HCT08N

Connections:
GND: C5.2, C6.2, C41.2, U3.14 (GND), U3.20 (~CS2), U4.14 (GND), U4.20 (~CS2), U90.7 (GND)
VCC: C5.1, C6.1, C41.1, JP6.1 (A), JP7.1 (A), R98.1, R99.2, U3.28 (VCC), U4.28 (VCC), U90.14 (VCC)
a0: U3.10 (A0), U4.10 (A0)
a1: U3.9 (A1), U4.9 (A1)
a2: U3.8 (A2), U4.8 (A2)
a3: U3.7 (A3), U4.7 (A3)
a4: U3.6 (A4), U4.6 (A4)
a5: U3.5 (A5), U4.5 (A5)
a6: U3.4 (A6), U4.4 (A6)
a7: U3.3 (A7), U4.3 (A7)
a8: U3.25 (A8), U4.25 (A8)
a9: U3.24 (A9), U4.24 (A9)
a10: U3.21 (A10), U4.21 (A10)
a11: U3.23 (A11), U4.23 (A11)
a12: U3.2 (A12), U4.2 (A12)
a13: U3.26 (A13), U4.26 (A13)
d0: U3.11 (D0), U4.11 (D0)
d1: U3.12 (D1), U4.12 (D1)
d2: U3.13 (D2), U4.13 (D2)
d3: U3.15 (D3), U4.15 (D3)
d4: U3.16 (D4), U4.16 (D4)
d5: U3.17 (D5), U4.17 (D5)
d6: U3.18 (D6), U4.18 (D6)
d7: U3.19 (D7), U4.19 (D7)
rom_a14: JP7.2 (C), U3.27 (CS3/A14), U4.27 (CS3/A14)
rom_a15: JP6.2 (C), U3.1 (NC/A15), U4.1 (NC/A15)
singlerom_a14: JP7.3 (B), U90.6
singlerom_a15: JP6.3 (B), U90.3, U90.12
singlerom_ce: JP13.2, U90.11
singlerom_ce_bas: JP8.3 (B), JP13.3
singlerom_ce_krn: JP5.3 (B), JP13.1
~BASIC_CS1: JP8.1 (A), U90.1
~FUNCHI_CS: U90.9
~FUNCLO_CS: U90.5, U90.10
~KERNAL_CS1: JP5.1 (A), U90.2, U90.4
~ce_basic_rom: JP8.2 (C), R98.2, U3.22 (~CS1)
~ce_krn_rom: JP5.2 (C), R99.1, U4.22 (~CS1)
~cef: U90.8, U90.13

Notes on the sheet:
|Range |Size |A15|A14| Content | |-----------|----------|---|---|---------| |$0000-$3FFF|16K | 0 | 0 | Kernal | |$4000-$7FFF|16K | 0 | 1 | Basic | |$8000-$BFFF|16K | 1 | 0 | FnLO | |$C000-$FFFF|16K | 1 | 1 | FnHI | A15 = /CEK & /CEB A14 = /CEK & /CEFL /CEF = /CEFL & /CEFH /CE = /CEK & /CEB & /CEF =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
