SukkoPera/LittleSixteen/sid.sch

## KiCad design sid.sch (2025-10-18)

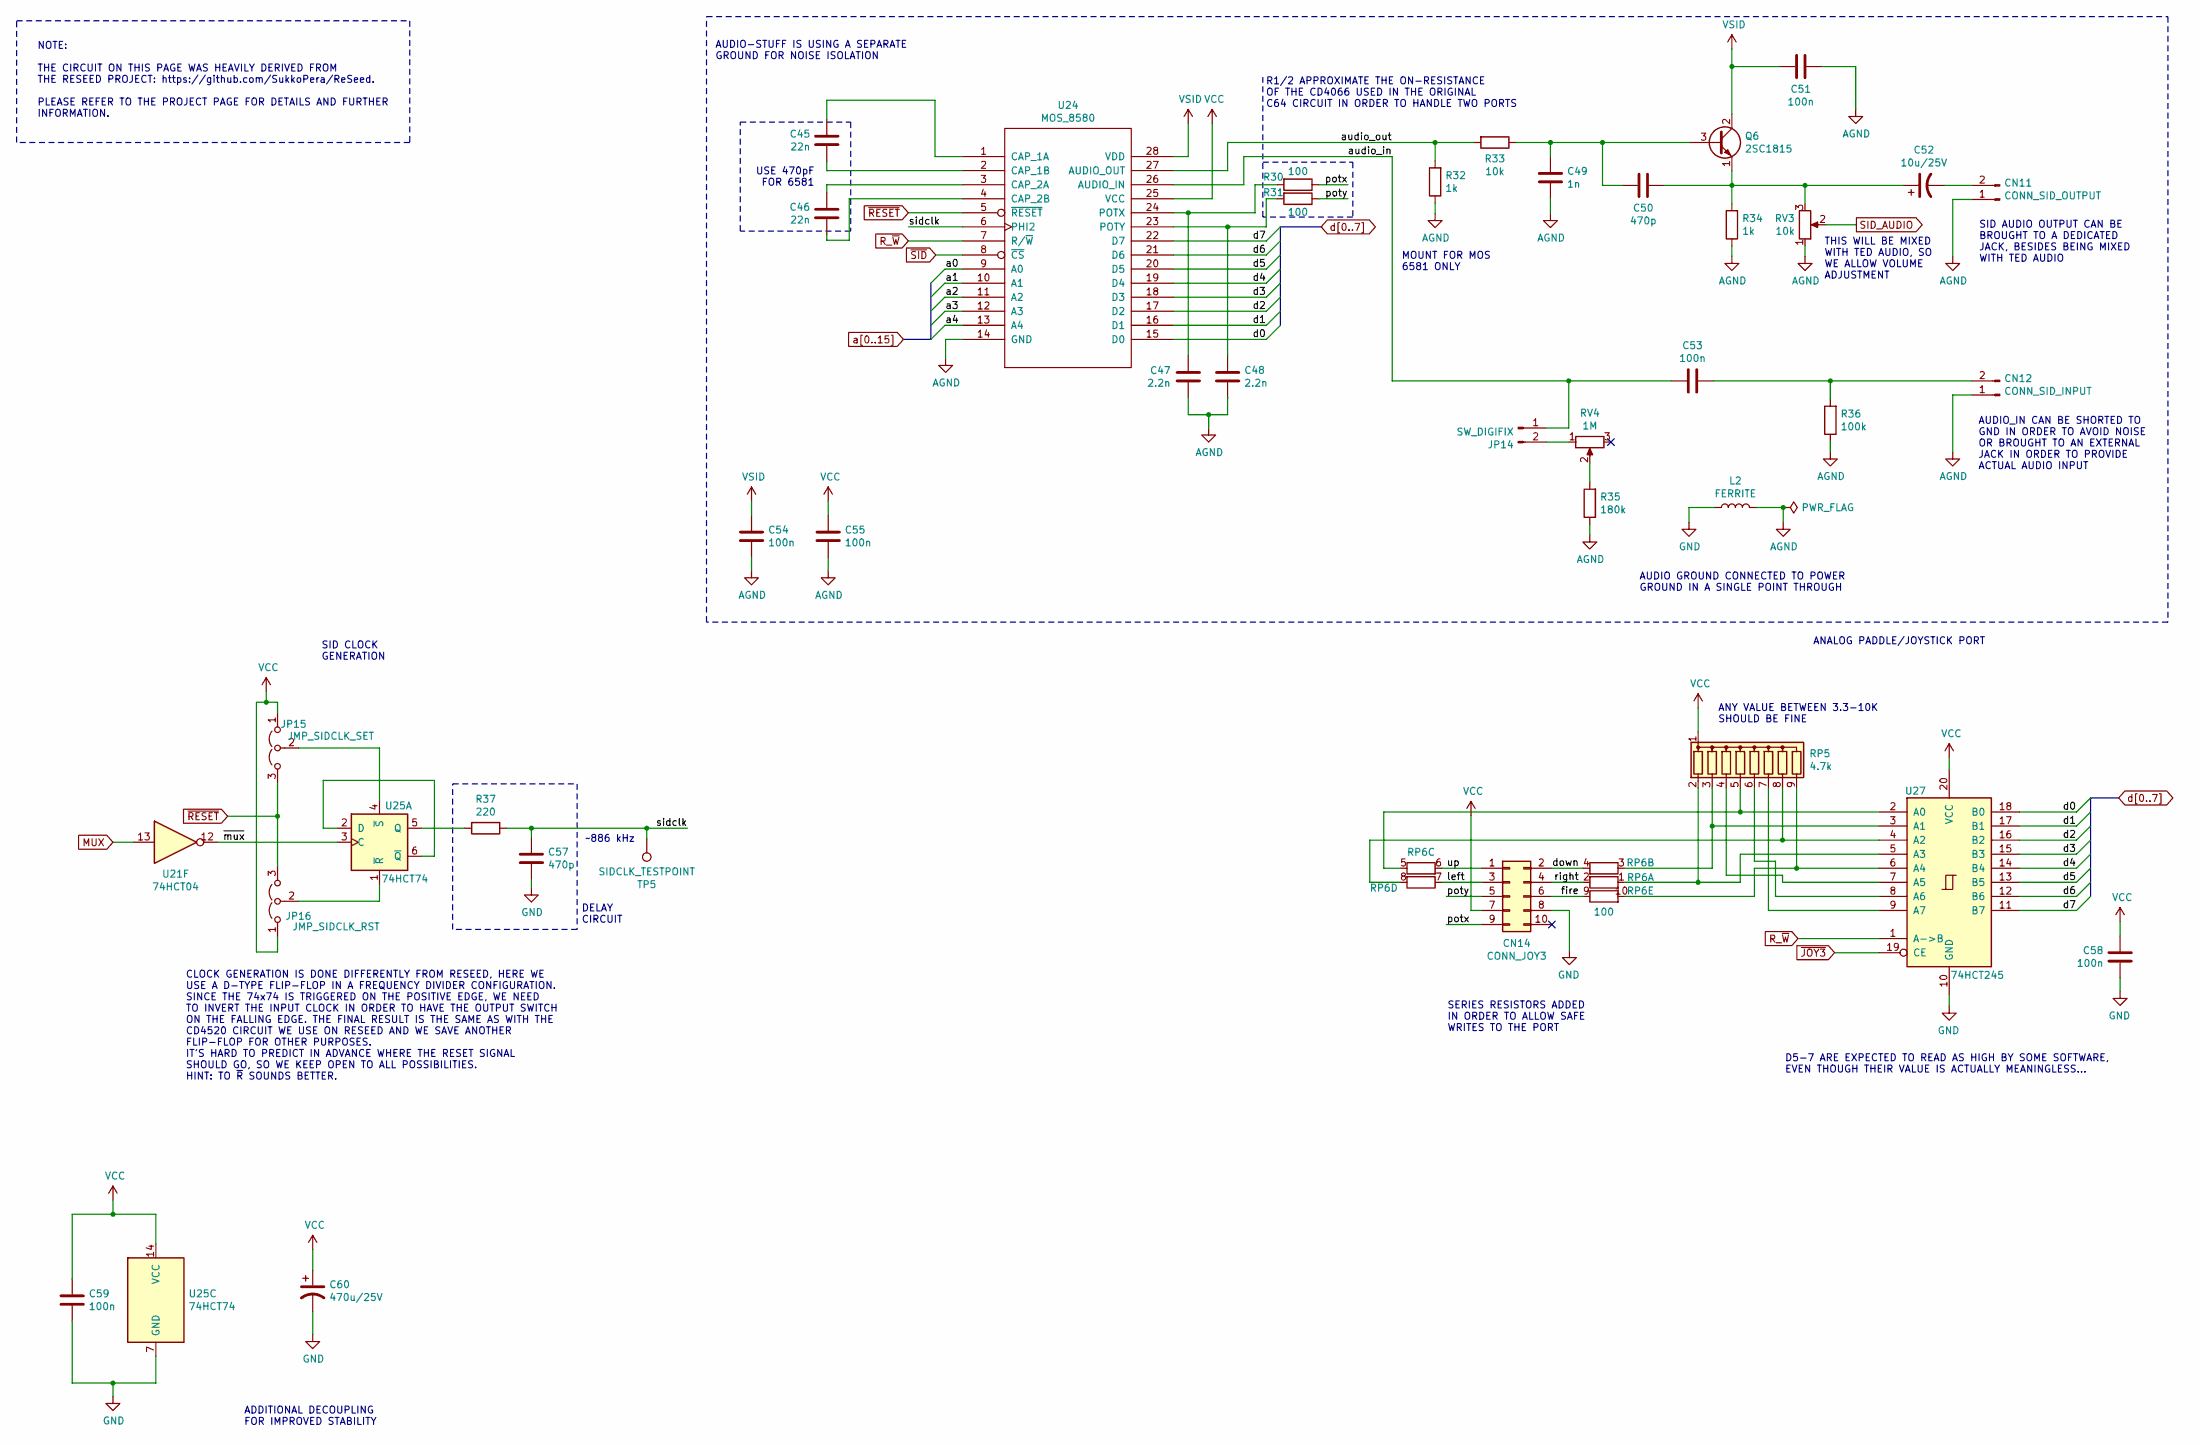
[picture p42: schematic sid.sch]

Parts:
C45, C46: 22n; C_Disc_D8.0mm_W2.5mm_P5.00mm; MouserPN 810-FG28X7R1H223KNT0
C47, C48: 2.2n; C_Disc_D8.0mm_W2.5mm_P5.00mm; MouserPN 810-FG28C0G1H222JNT6
C49: 1n; C_Disc_D8.0mm_W2.5mm_P5.00mm; MouserPN 810-FG28C0G1H102JNT6
C50, C57: 470p; C_Disc_D8.0mm_W2.5mm_P5.00mm; MouserPN 810-FG28C0G1H471JNT6
C51, C53, C54, C55, C58, C59: 100n; C_Disc_D8.0mm_W2.5mm_P5.00mm; MouserPN 810-FG28X7R1H104KNT0
C52: 10u/25V; CP_Radial_D5.0mm_P2.00mm; MouserPN 710-860010572002
C60: 470u/25V; CP_Radial_D8.0mm_P3.50mm; MouserPN 710-860010474013
CN11: CONN_SID_OUTPUT; PinHeader_1x02_P2.54mm_Vertical
CN12: CONN_SID_INPUT; PinHeader_1x02_P2.54mm_Vertical
CN14: CONN_JOY3; PinHeader_2x05_P2.54mm_Vertical
JP14: SW_DIGIFIX; PinHeader_1x02_P2.54mm_Vertical
JP15: JMP_SIDCLK_SET; SolderJumper-3_P1.3mm_Open_RoundedPad1.0x1.5mm; MouserPN ---
JP16: JMP_SIDCLK_RST; SolderJumper-3_P1.3mm_Open_RoundedPad1.0x1.5mm; MouserPN ---
L2: FERRITE; L_Radial_D6.0mm_P4.00mm; MouserPN 875-28C0236-0EW-10
Q6: 2SC1815; TO-92_Inline_Wide; MouserPN 610-2SC1815-GR
R30, R31: 100; R_Axial_DIN0207_L6.3mm_D2.5mm_P5.08mm_Vertical; MouserPN 708-RNF14FTD100R
R32, R34: 1k; R_Axial_DIN0207_L6.3mm_D2.5mm_P5.08mm_Vertical; MouserPN 603-MFR-25FBF52-1K
R33: 10k; R_Axial_DIN0207_L6.3mm_D2.5mm_P5.08mm_Vertical; MouserPN 603-MFR-25FTF52-10K
R35: 180k; R_Axial_DIN0207_L6.3mm_D2.5mm_P5.08mm_Vertical; MouserPN 603-MF0207FTE52-180K
R36: 100k; R_Axial_DIN0207_L6.3mm_D2.5mm_P5.08mm_Vertical; MouserPN 603-MFR-25FBF52-100K
R37: 220; R_Axial_DIN0207_L6.3mm_D2.5mm_P5.08mm_Vertical
RP5: 4.7k; R_Array_SIP9
RP6: 100; R_Array_SIP10; MouserPN 652-4610X-2LF-100
RV3: 10k; Potentiometer_Bourns_3296W_Vertical; MouserPN 652-3296W-1-103LF
RV4: 1M; Potentiometer_Bourns_3296W_Vertical; MouserPN 652-3296W-1-105LF
TP5: SIDCLK_TESTPOINT; TestPoint_Pad_D2.0mm; MouserPN ---
U21: 74HCT04; DIP-14_W7.62mm_Socket_LongPads; MouserPN 595-SN74HCT04N
U24: MOS_8580; DIP-28_W15.24mm_Socket_LongPads; MouserPN :)
U25: 74HCT74; DIP-14_W7.62mm_Socket_LongPads; MouserPN 595-SN74HC74N
U27: 74HCT245; DIP-20_W7.62mm_Socket_LongPads; MouserPN 595-SN74HCT245N

Connections:
AGND: C47.2, C48.2, C49.2, C51.1, C54.2, C55.2, CN11.1, CN12.1, L2.2, R32.1, R34.1, R35.1, R36.1, RV3.1, U24.14 (GND)
GND: C57.2, C58.2, C59.2, C60.2, CN14.8, L2.1, U25.7 (GND), U27.10 (GND)
MUX: U21.13
unnamed: C45.1, U24.1 (CAP_1A)
unnamed: C45.2, U24.2 (CAP_1B)
unnamed: C46.1, U24.3 (CAP_2A)
unnamed: C46.2, U24.4 (CAP_2B)
unnamed: C47.1, R30.2, U24.24 (POTX)
unnamed: C48.1, R31.2, U24.23 (POTY)
unnamed: C49.1, C50.2, Q6.3 (B), R33.1
unnamed: C50.1, C52.1, Q6.1 (E), R34.2, RV3.3
unnamed: C52.2, CN11.2
unnamed: C53.1, CN12.2, R36.2
unnamed: JP14.2, RV4.1
unnamed: JP15.2 (C), U25.4 (~S)
unnamed: JP16.2 (C), U25.1 (~R)
unnamed: R35.2, RV4.2
unnamed: R37.2, U25.5 (Q)
unnamed: RP5.2 (R1), RP6.1 (R1.1), U27.5 (A3)
unnamed: RP5.3 (R2), RP6.3 (R2.1), U27.3 (A1)
unnamed: RP5.4 (R3), U27.7 (A5)
unnamed: RP5.5 (R4), RP6.5 (R3.1), U27.2 (A0)
unnamed: RP5.6 (R5), U27.8 (A6)
unnamed: RP5.7 (R6), U27.9 (A7)
unnamed: RP5.8 (R7), RP6.8 (R4.2), U27.4 (A2)
unnamed: RP5.9 (R8), RP6.10 (R5.2), U27.6 (A4)
unnamed: U25.2 (D), U25.6 (~Q)
R_~W: U24.7 (R/~W), U27.1 (A->B)
SID_AUDIO: RV3.2
VCC: C55.1, C58.1, C59.1, C60.1, CN14.7, JP15.1 (A), JP16.1 (A), RP5.1 (common), U24.25 (VCC), U25.14 (VCC), U27.20 (VCC)
VSID: C51.2, C54.1, Q6.2 (C), U24.28 (VDD)
a0: U24.9 (A0)
a1: U24.10 (A1)
a2: U24.11 (A2)
a3: U24.12 (A3)
a4: U24.13 (A4)
audio_in: C53.2, JP14.1, U24.26 (AUDIO_IN)
audio_out: R32.2, R33.2, U24.27 (AUDIO_OUT)
d0: U24.15 (D0), U27.18 (B0)
d1: U24.16 (D1), U27.17 (B1)
d2: U24.17 (D2), U27.16 (B2)
d3: U24.18 (D3), U27.15 (B3)
d4: U24.19 (D4), U27.14 (B4)
d5: U24.20 (D5), U27.13 (B5)
d6: U24.21 (D6), U27.12 (B6)
d7: U24.22 (D7), U27.11 (B7)
down: CN14.2, RP6.4 (R2.2)
fire: CN14.6, RP6.9 (R5.1)
left: CN14.3, RP6.7 (R4.1)
potx: CN14.9, R30.1
poty: CN14.5, R31.1
right: CN14.4, RP6.2 (R1.2)
sidclk: C57.1, R37.1, TP5.1, U24.6 (PHI2)
up: CN14.1, RP6.6 (R3.2)
~JOY3: U27.19 (CE)
~RESET: JP15.3 (B), JP16.3 (B), U24.5 (~RESET)
~SID: U24.8 (~CS)
~mux: U21.12, U25.3 (C)

Notes on the sheet:
ANALOG PADDLE/JOYSTICK PORT
D5-7 ARE EXPECTED TO READ AS HIGH BY SOME SOFTWARE, EVEN THOUGH THEIR VALUE IS ACTUALLY MEANINGLESS...
AUDIO_IN CAN BE SHORTED TO GND IN ORDER TO AVOID NOISE OR BROUGHT TO AN EXTERNAL JACK IN ORDER TO PROVIDE ACTUAL AUDIO INPUT
USE 470pF FOR 6581
ADDITIONAL DECOUPLING FOR IMPROVED STABILITY
MOUNT FOR MOS 6581 ONLY
SID CLOCK GENERATION
SERIES RESISTORS ADDED IN ORDER TO ALLOW SAFE WRITES TO THE PORT
AUDIO-STUFF IS USING A SEPARATE GROUND FOR NOISE ISOLATION
AUDIO GROUND CONNECTED TO POWER GROUND IN A SINGLE POINT THROUGH
ANY VALUE BETWEEN 3.3-10K SHOULD BE FINE
R1/2 APPROXIMATE THE ON-RESISTANCE OF THE CD4066 USED IN THE ORIGINAL C64 CIRCUIT IN ORDER TO HANDLE TWO PORTS
DELAY CIRCUIT
~~886 kHz
CLOCK GENERATION IS DONE DIFFERENTLY FROM RESEED, HERE WE USE A D-TYPE FLIP-FLOP IN A FREQUENCY DIVIDER CONFIGURATION. SINCE THE 74x74 IS TRIGGERED ON THE POSITIVE EDGE, WE NEED TO INVERT THE INPUT CLOCK IN ORDER TO HAVE THE OUTPUT SWITCH ON THE FALLING EDGE. THE FINAL RESULT IS THE SAME AS WITH TH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
NOTE: THE CIRCUIT ON THIS PAGE WAS HEAVILY DERIVED FROM THE RESEED PROJECT: https://github.com/SukkoPera/ReSeed. PLEASE REFER TO THE PROJECT PAGE FOR DETAILS AND FURTHER INFORMATION.
SID AUDIO OUTPUT CAN BE BROUGHT TO A DEDICATED JACK, BESIDES BEING MIXED WITH TED AUDIO
THIS WILL BE MIXED WITH TED AUDIO, SO WE ALLOW VOLUME ADJUSTMENT
