SukkoPera/LittleSixteen/ted.sch

## KiCad design ted.sch (2025-10-18)

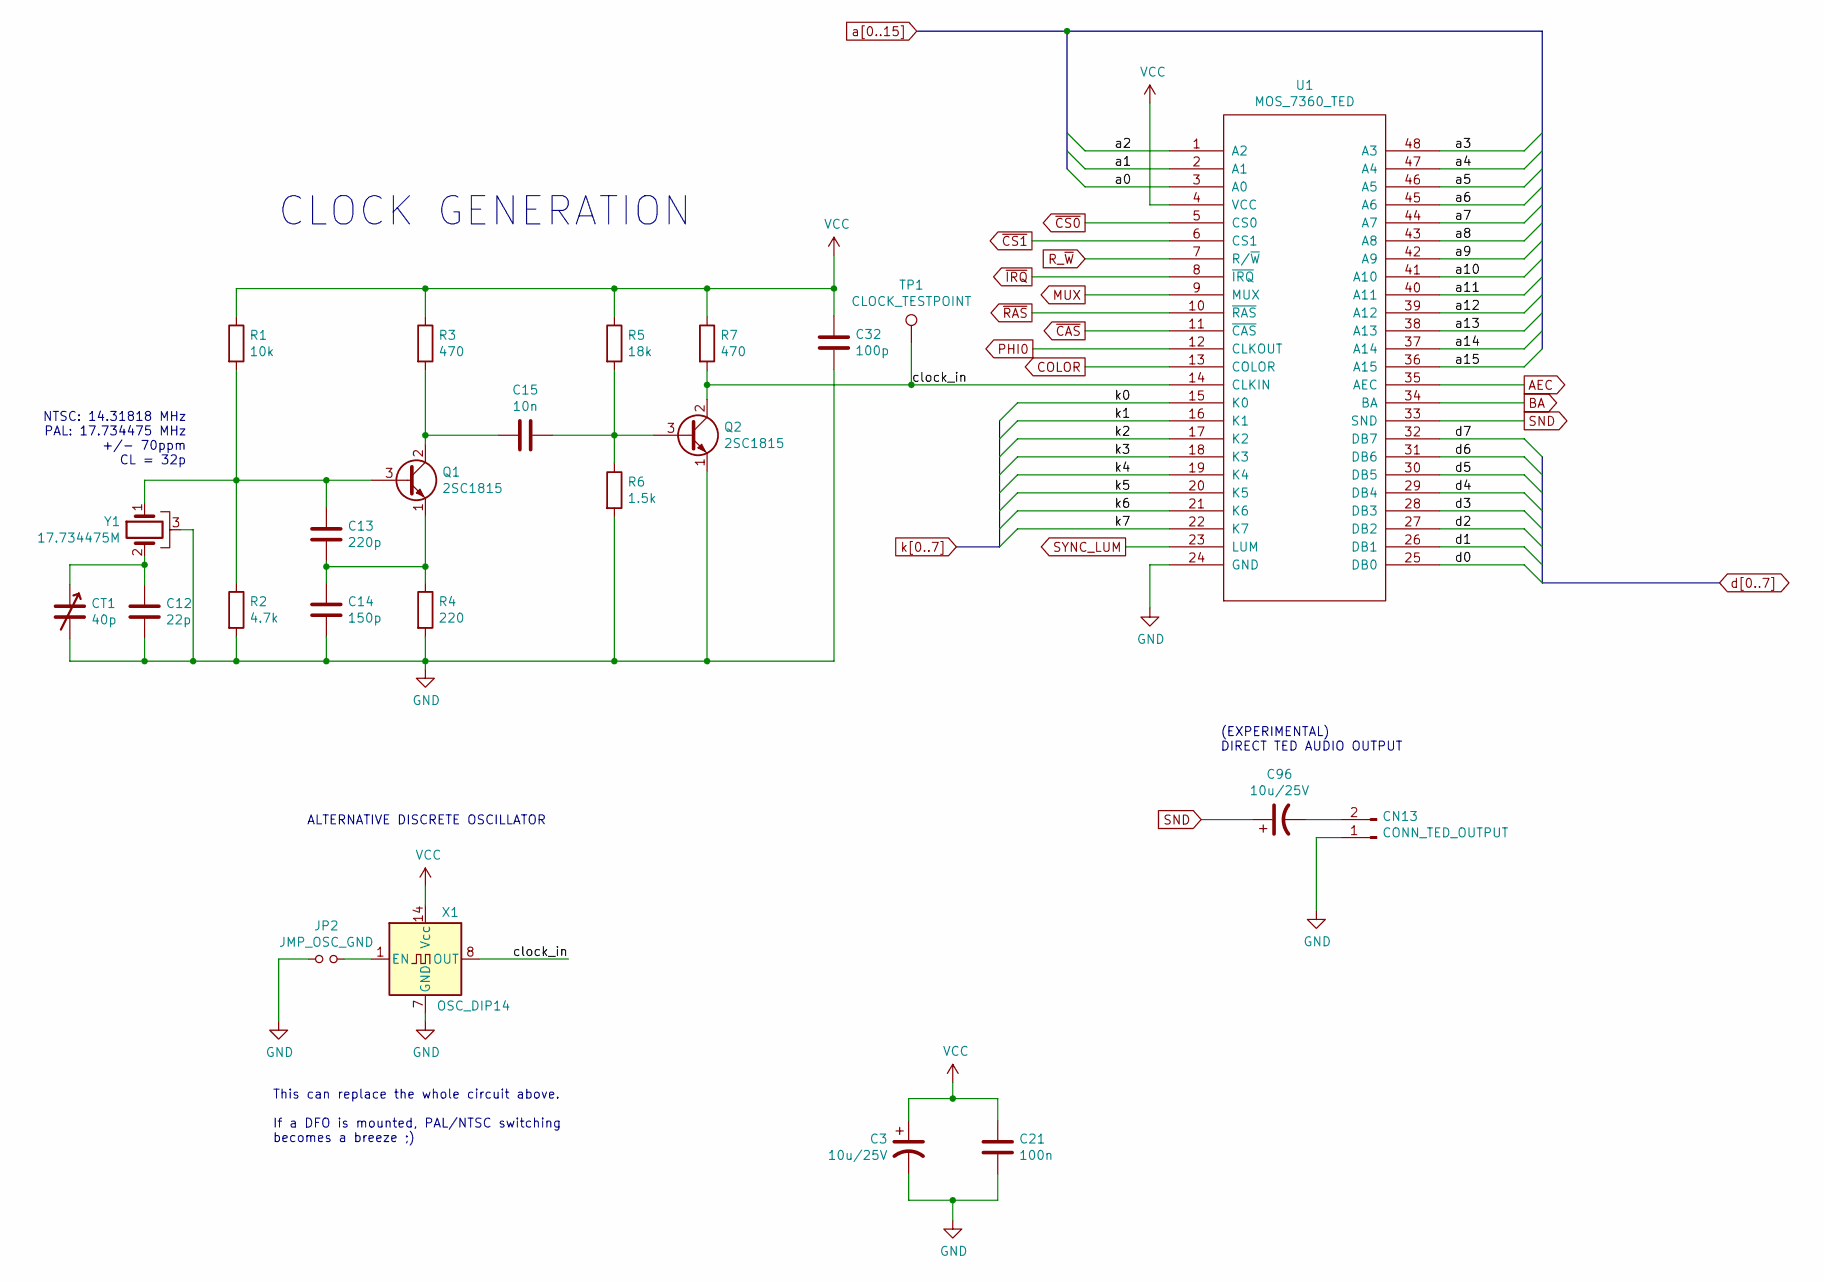
[picture p43: schematic ted.sch]

Parts:
C3, C96: 10u/25V; CP_Radial_D5.0mm_P2.00mm; MouserPN 710-860010572002
C12: 22p; C_Disc_D8.0mm_W2.5mm_P5.00mm
C13: 220p; C_Disc_D8.0mm_W2.5mm_P5.00mm
C14: 150p; C_Disc_D8.0mm_W2.5mm_P5.00mm
C15: 10n; C_Disc_D8.0mm_W2.5mm_P5.00mm
C21: 100n; C_Disc_D8.0mm_W2.5mm_P5.00mm; MouserPN 810-FG28X7R1H104KNT0
C32: 100p; C_Disc_D8.0mm_W2.5mm_P5.00mm; MouserPN 810-FG28C0G2A101JNT6
CN13: CONN_TED_OUTPUT; PinHeader_1x02_P2.54mm_Vertical
CT1: 40p; VariCap
JP2: JMP_OSC_GND; SolderJumper-2_P1.3mm_Open_RoundedPad1.0x1.5mm; MouserPN ---
Q1, Q2: 2SC1815; TO-92_Inline_Wide; MouserPN 610-2SC1815-GR
R1: 10k; R_Axial_DIN0207_L6.3mm_D2.5mm_P5.08mm_Vertical; MouserPN 603-MFR-25FTF52-10K
R2: 4.7k; R_Axial_DIN0207_L6.3mm_D2.5mm_P5.08mm_Vertical
R3, R7: 470; R_Axial_DIN0207_L6.3mm_D2.5mm_P5.08mm_Vertical
R4: 220; R_Axial_DIN0207_L6.3mm_D2.5mm_P5.08mm_Vertical
R5: 18k; R_Axial_DIN0207_L6.3mm_D2.5mm_P5.08mm_Vertical
R6: 1.5k; R_Axial_DIN0207_L6.3mm_D2.5mm_P5.08mm_Vertical
TP1: CLOCK_TESTPOINT; TestPoint_Pad_D2.0mm; MouserPN ---
U1: MOS_7360_TED; DIP-48_W15.24mm_Socket_LongPads; MouserPN :)
X1: OSC_DIP14; Oscillator_DIP-8+14
Y1: 17.734475M; Crystal_HC49-U_Horizontal_1EP_style2; MouserPN 710-830003298B

Connections:
AEC: U1.35 (AEC)
BA: U1.34 (BA)
COLOR: U1.13 (COLOR)
GND: C3.2, C12.2, C14.2, C21.2, C32.2, CN13.1, CT1.2, JP2.1, Q2.1 (E), R2.2, R4.2, R6.2, U1.24 (GND), X1.7 (GND), Y1.3
MUX: U1.9 (MUX)
unnamed: C12.1, CT1.1, Y1.2
unnamed: C13.1, Q1.3 (B), R1.2, R2.1, Y1.1
unnamed: C13.2, C14.1, Q1.1 (E), R4.1
unnamed: C15.1, Q2.3 (B), R5.2, R6.1
unnamed: C15.2, Q1.2 (C), R3.2
unnamed: C96.2, CN13.2
unnamed: JP2.2, X1.1 (EN)
PHI0: U1.12 (CLKOUT)
R_~W: U1.7 (R/~W)
SND: C96.1, U1.33 (SND)
SYNC_LUM: U1.23 (LUM)
VCC: C3.1, C21.1, C32.1, R1.1, R3.1, R5.1, R7.1, U1.4 (VCC), X1.14 (Vcc)
a0: U1.3 (A0)
a1: U1.2 (A1)
a2: U1.1 (A2)
a3: U1.48 (A3)
a4: U1.47 (A4)
a5: U1.46 (A5)
a6: U1.45 (A6)
a7: U1.44 (A7)
a8: U1.43 (A8)
a9: U1.42 (A9)
a10: U1.41 (A10)
a11: U1.40 (A11)
a12: U1.39 (A12)
a13: U1.38 (A13)
a14: U1.37 (A14)
a15: U1.36 (A15)
clock_in: Q2.2 (C), R7.2, TP1.1, U1.14 (CLKIN), X1.8 (OUT)
d0: U1.25 (DB0)
d1: U1.26 (DB1)
d2: U1.27 (DB2)
d3: U1.28 (DB3)
d4: U1.29 (DB4)
d5: U1.30 (DB5)
d6: U1.31 (DB6)
d7: U1.32 (DB7)
k0: U1.15 (K0)
k1: U1.16 (K1)
k2: U1.17 (K2)
k3: U1.18 (K3)
k4: U1.19 (K4)
k5: U1.20 (K5)
k6: U1.21 (K6)
k7: U1.22 (K7)
~CAS: U1.11 (~CAS)
~CS0: U1.5 (CS0)
~CS1: U1.6 (CS1)
~IRQ: U1.8 (~IRQ)
~RAS: U1.10 (~RAS)

Notes on the sheet:
NTSC: 14.31818 MHz PAL: 17.734475 MHz +/- 70ppm CL = 32p
CLOCK GENERATION
(EXPERIMENTAL) DIRECT TED AUDIO OUTPUT
This can replace the whole circuit above. If a DFO is mounted, PAL/NTSC switching becomes a breeze ;)
ALTERNATIVE DISCRETE OSCILLATOR
