SukkoPera/LittleSixteen/userport.sch

## KiCad design userport.sch (2025-10-18)

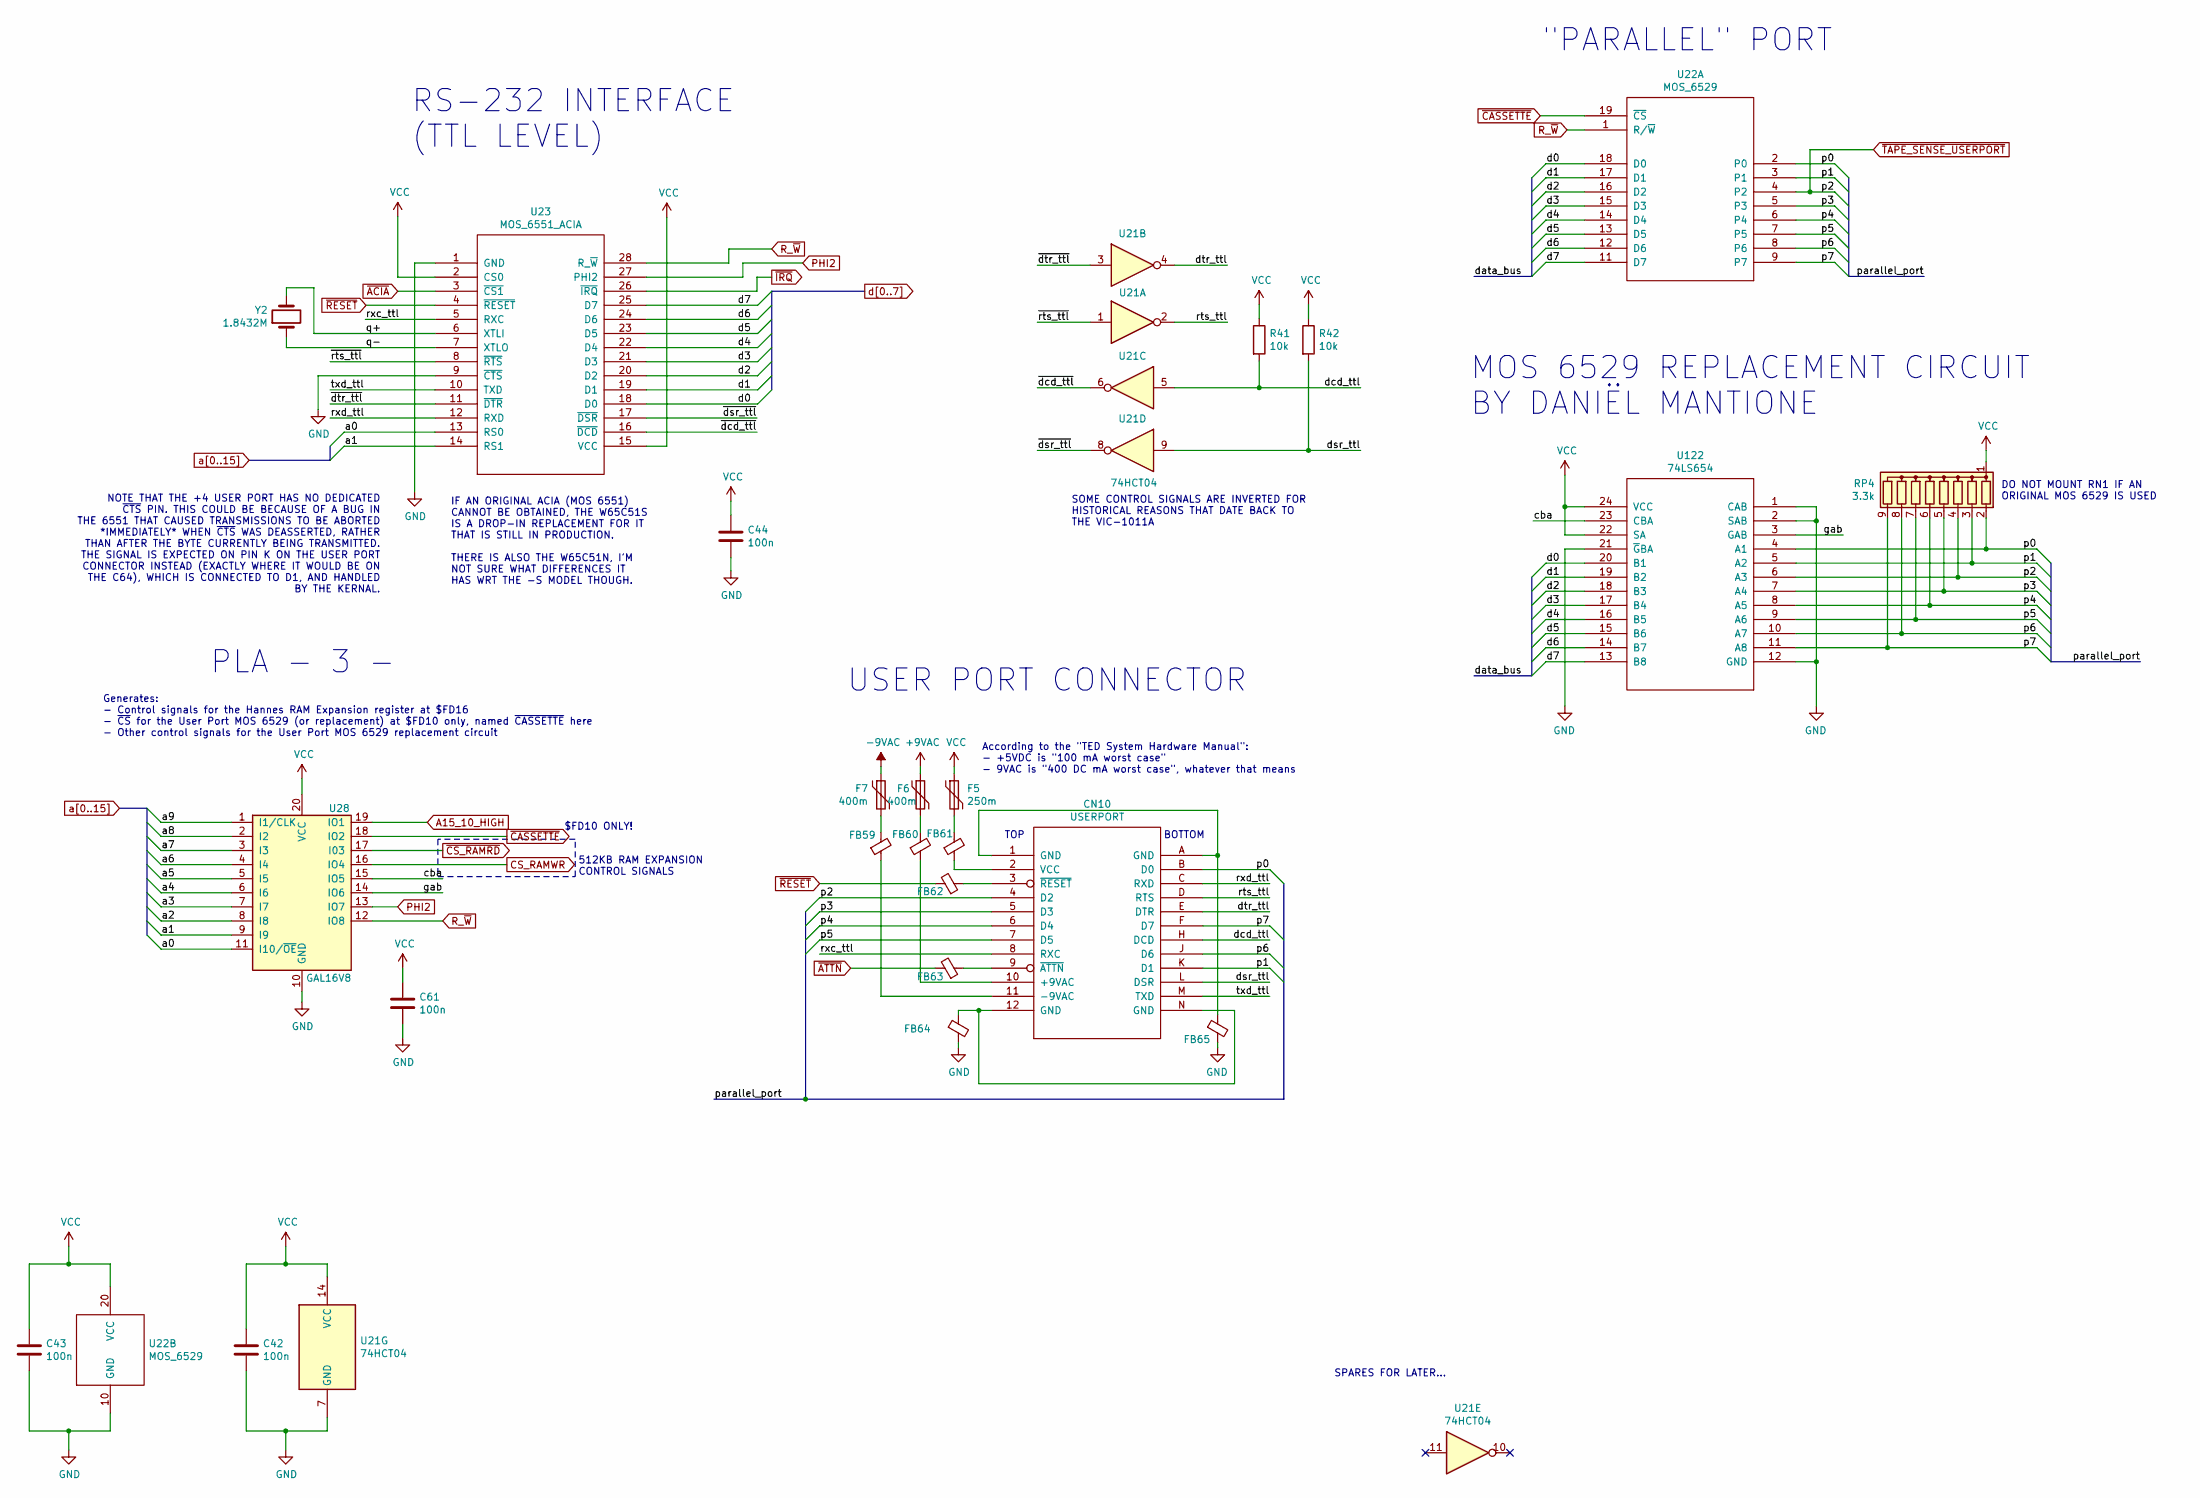
[picture p44: schematic userport.sch]

Parts:
C42, C43, C44, C61: 100n; C_Disc_D8.0mm_W2.5mm_P5.00mm; MouserPN 810-FG28X7R1H104KNT0
CN10: USERPORT; Plus4_UserPort; MouserPN ---
F5: 250m; Fuse_Bourns; MouserPN 603-BK60-025-DZ
F6, F7: 400m; Fuse_Bourns; MouserPN 603-BK60-040-DI
FB59, FB60, FB61, FB62, FB63, FB64, FB65: FERRITE; EMI_Filter; MouserPN 623-2743015112
R41, R42: 10k; R_Axial_DIN0207_L6.3mm_D2.5mm_P5.08mm_Vertical; MouserPN 603-MFR-25FTF52-10K
RP4: 3.3k; R_Array_SIP9
U21: 74HCT04; DIP-14_W7.62mm_Socket_LongPads; MouserPN 595-SN74HCT04N
U22: MOS_6529; DIP-20_W7.62mm_Socket_LongPads; MouserPN :)
U23: MOS_6551_ACIA; DIP-28_W15.24mm_Socket_LongPads; MouserPN :)
U28: GAL16V8; DIP-20_W7.62mm_Socket_LongPads; MouserPN 556-AF16V8B15PU
U122: 74LS654; DIP-24_W7.62mm_Socket_LongPads
Y2: 1.8432M; Crystal_HC49-U_Vertical; MouserPN 520-HCA184-SX

Connections:
+9VAC: F6.1
-9VAC: F7.1
A15_10_HIGH: U28.19 (IO1)
CS_RAMWR: U28.16 (IO4)
GND: C42.2, C43.2, C44.2, C61.2, FB64.2, FB65.2, U21.7 (GND), U22.10 (GND), U23.1 (GND), U23.9 (~CTS), U28.10 (GND), U122.1 (CAB), U122.2 (SAB), U122.12 (GND), U122.21 (~G~BA)
unnamed: CN10.1 (GND), CN10.A (GND), FB65.1
unnamed: CN10.2 (VCC), FB61.1
unnamed: CN10.3 (~RESET), FB62.1
unnamed: CN10.9 (~ATTN), FB63.1
unnamed: CN10.10 (+9VAC), FB60.1
unnamed: CN10.11 (-9VAC), FB59.1
unnamed: CN10.12 (GND), CN10.N (GND), FB64.1
unnamed: F5.2, FB61.2
unnamed: F6.2, FB60.2
unnamed: F7.2, FB59.2
PHI2: U23.27 (PHI2), U28.13 (IO7)
R_~W: U22.1 (R/~W), U23.28 (R_~W), U28.12 (IO8)
VCC: C42.1, C43.1, C44.1, C61.1, F5.1, R41.1, R42.1, RP4.1 (common), U21.14 (VCC), U22.20 (VCC), U23.2 (CS0), U23.15 (VCC), U28.20 (VCC), U122.22 (SA), U122.24 (VCC)
a0: U23.13 (RS0), U28.11 (I10/~OE~)
a1: U23.14 (RS1), U28.9 (I9)
a2: U28.8 (I8)
a3: U28.7 (I7)
a4: U28.6 (I6)
a5: U28.5 (I5)
a6: U28.4 (I4)
a7: U28.3 (I3)
a8: U28.2 (I2)
a9: U28.1 (I1/CLK)
cba: U28.15 (IO5), U122.23 (CBA)
d0: U22.18 (D0), U23.18 (D0), U122.20 (B1)
d1: U22.17 (D1), U23.19 (D1), U122.19 (B2)
d2: U22.16 (D2), U23.20 (D2), U122.18 (B3)
d3: U22.15 (D3), U23.21 (D3), U122.17 (B4)
d4: U22.14 (D4), U23.22 (D4), U122.16 (B5)
d5: U22.13 (D5), U23.23 (D5), U122.15 (B6)
d6: U22.12 (D6), U23.24 (D6), U122.14 (B7)
d7: U22.11 (D7), U23.25 (D7), U122.13 (B8)
dcd_ttl: CN10.H (DCD), R41.2, U21.5
dsr_ttl: CN10.L (DSR), R42.2, U21.9
dtr_ttl: CN10.E (DTR), U21.4
gab: U28.14 (IO6), U122.3 (GAB)
p0: CN10.B (D0), RP4.2 (R1), U22.2 (P0), U122.4 (A1)
p1: CN10.K (D1), RP4.3 (R2), U22.3 (P1), U122.5 (A2)
p3: CN10.5 (D3), RP4.5 (R4), U22.5 (P3), U122.7 (A4)
p4: CN10.6 (D4), RP4.6 (R5), U22.6 (P4), U122.8 (A5)
p5: CN10.7 (D5), RP4.7 (R6), U22.7 (P5), U122.9 (A6)
p6: CN10.J (D6), RP4.8 (R7), U22.8 (P6), U122.10 (A7)
p7: CN10.F (D7), RP4.9 (R8), U22.9 (P7), U122.11 (A8)
q+: U23.6 (XTLI), Y2.2
q-: U23.7 (XTLO), Y2.1
rts_ttl: CN10.D (RTS), U21.2
rxc_ttl: CN10.8 (RXC), U23.5 (RXC)
rxd_ttl: CN10.C (RXD), U23.12 (RXD)
txd_ttl: CN10.M (TXD), U23.10 (TXD)
~ACIA: U23.3 (~CS1)
~ATTN: FB63.2
~CASSETTE: U22.19 (~CS), U28.18 (IO2)
~CS_RAMRD: U28.17 (I03)
~IRQ: U23.26 (~IRQ)
~RESET: FB62.2, U23.4 (~RESET)
~TAPE_SENSE_USERPORT: CN10.4 (D2), RP4.4 (R3), U22.4 (P2), U122.6 (A3)
~dcd_ttl: U21.6, U23.16 (~DCD)
~dsr_ttl: U21.8, U23.17 (~DSR)
~dtr_ttl: U21.3, U23.11 (~DTR)
~rts_ttl: U21.1, U23.8 (~RTS)

Notes on the sheet:
"PARALLEL" PORT
USER PORT CONNECTOR
NOTE THAT THE +4 USER PORT HAS NO DEDICATED ~CTS~ PIN. THIS COULD BE BECAUSE OF A BUG IN THE 6551 THAT CAUSED TRANSMISSIONS TO BE ABORTED *IMMEDIATELY* WHEN ~CTS~ WAS DEASSERTED, RATHER THAN AFTER THE BYTE CURRENTLY BEING TRANSMITTED. THE SIGNAL IS EXPECTED ON PIN K ON THE USER PORT CONNECTOR INSTE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
IF AN ORIGINAL ACIA (MOS 6551) CANNOT BE OBTAINED, THE W65C51S IS A DROP-IN REPLACEMENT FOR IT THAT IS STILL IN PRODUCTION. THERE IS ALSO THE W65C51N, I'M NOT SURE WHAT DIFFERENCES IT HAS WRT THE -S MODEL THOUGH.
RS-232 INTERFACE (TTL LEVEL)
TOP
BOTTOM
MOS 6529 REPLACEMENT CIRCUIT BY DANIËL MANTIONE
DO NOT MOUNT RN1 IF AN ORIGINAL MOS 6529 IS USED
SOME CONTROL SIGNALS ARE INVERTED FOR HISTORICAL REASONS THAT DATE BACK TO THE VIC-1011A
SPARES FOR LATER...
According to the "TED System Hardware Manual": - +5VDC is "100 mA worst case" - 9VAC is "400 DC mA worst case", whatever that means
$FD10 ONLY!
PLA - 3 -
512KB RAM EXPANSION CONTROL SIGNALS
Generates: - Control signals for the Hannes RAM Expansion register at $FD16 - ~CS~ for the User Port MOS 6529 (or replacement) at $FD10 only, named ~CASSETTE~ here - Other control signals for the User Port MOS 6529 replacement circuit
